iotvertebrae/modules/hardware/pcbDesign/fabAdcRib/pdf/rib4inAd_00-B_Silkscreen.pdf

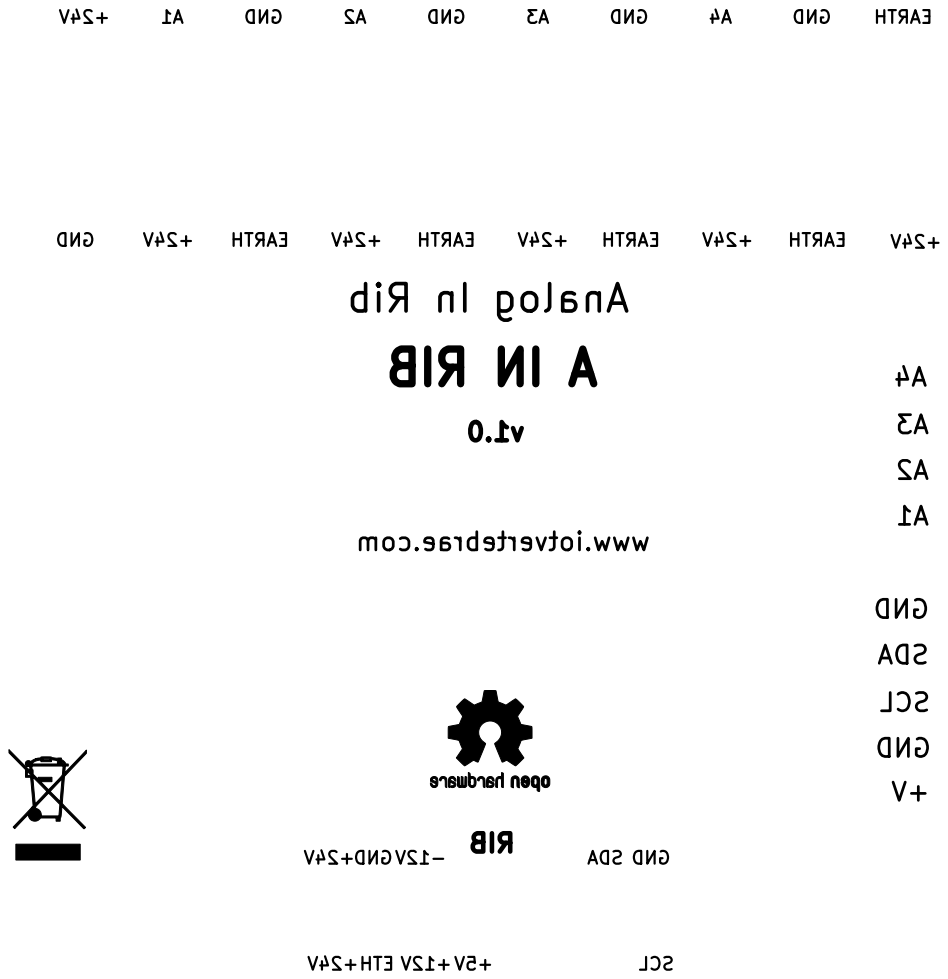
[picture p6: page 1]

GND EARTH A4 SDA GND

GND +VGND Analog In Rib
