iotvertebrae/modules/hardware/pcbDesign/fabAnalogVertebra/pdf/vertExpI2c_00-B_Silkscreen.pdf

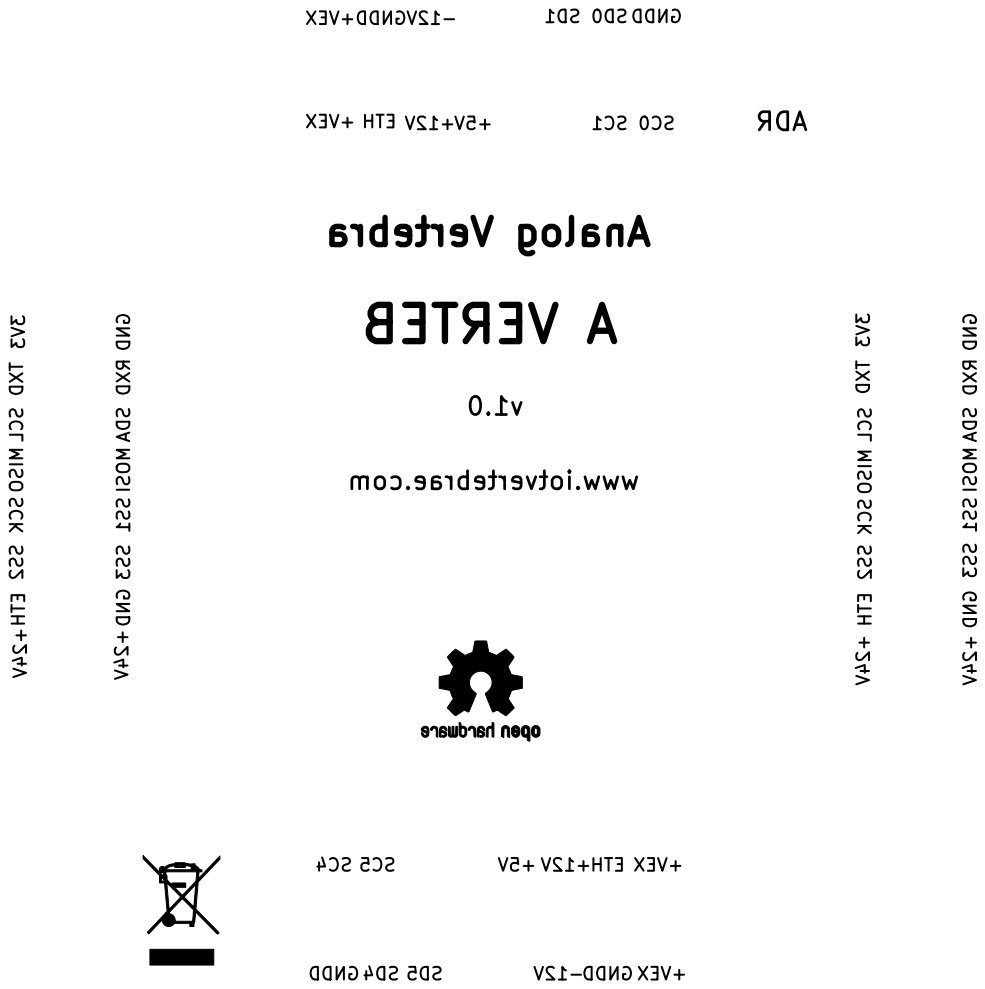
[picture p7: page 1]

+VEX A VERTEB GND ETH SS1 +VEX RXD SS2 GNDD 3V3 3V3 +24V GNDD MOSI SDA TXD +24V ADR

Analog Vertebra MOSI SCL www.iotvertebrae.com
