iotvertebrae/modules/hardware/pcbDesign/fabDacRib/pdf/rib4outAd_00-B_Silkscreen.pdf

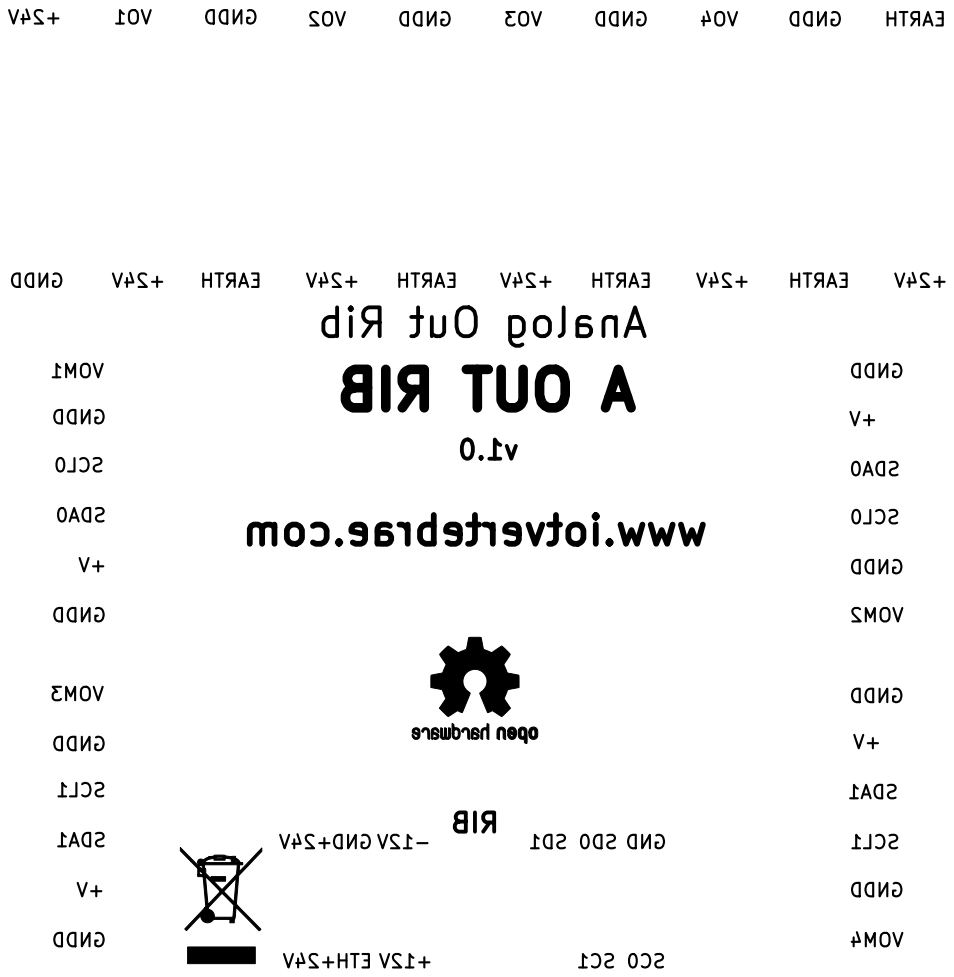
[picture p8: page 1]

SD1 SCL0 GNDD Analog Out Rib

ETH www.iotvertebrae.com
