iotvertebrae/modules/hardware/pcbDesign/v2.0/gerbers/avert20/pdf/avert_12-B_Silkscreen.pdf

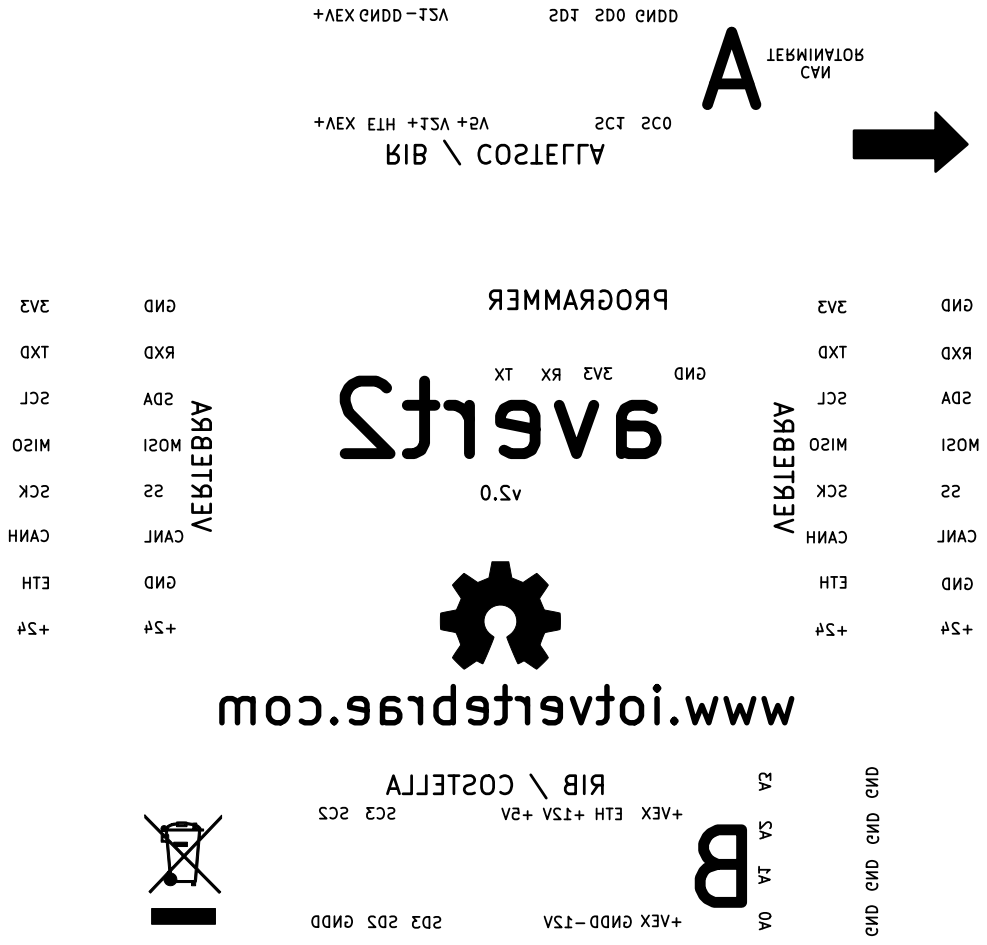
[picture p9: page 1]

+VEX PROGRAMMER GND GND

COSTELLA / RIB VERTEBRA VERTEBRA

+12V A2 GNDD www.iotvertebrae.com
