iotvertebrae/modules/hardware/pcbDesign/fabDigitalInputRib/pdf/rib8in_00-Edge_Cuts.pdf

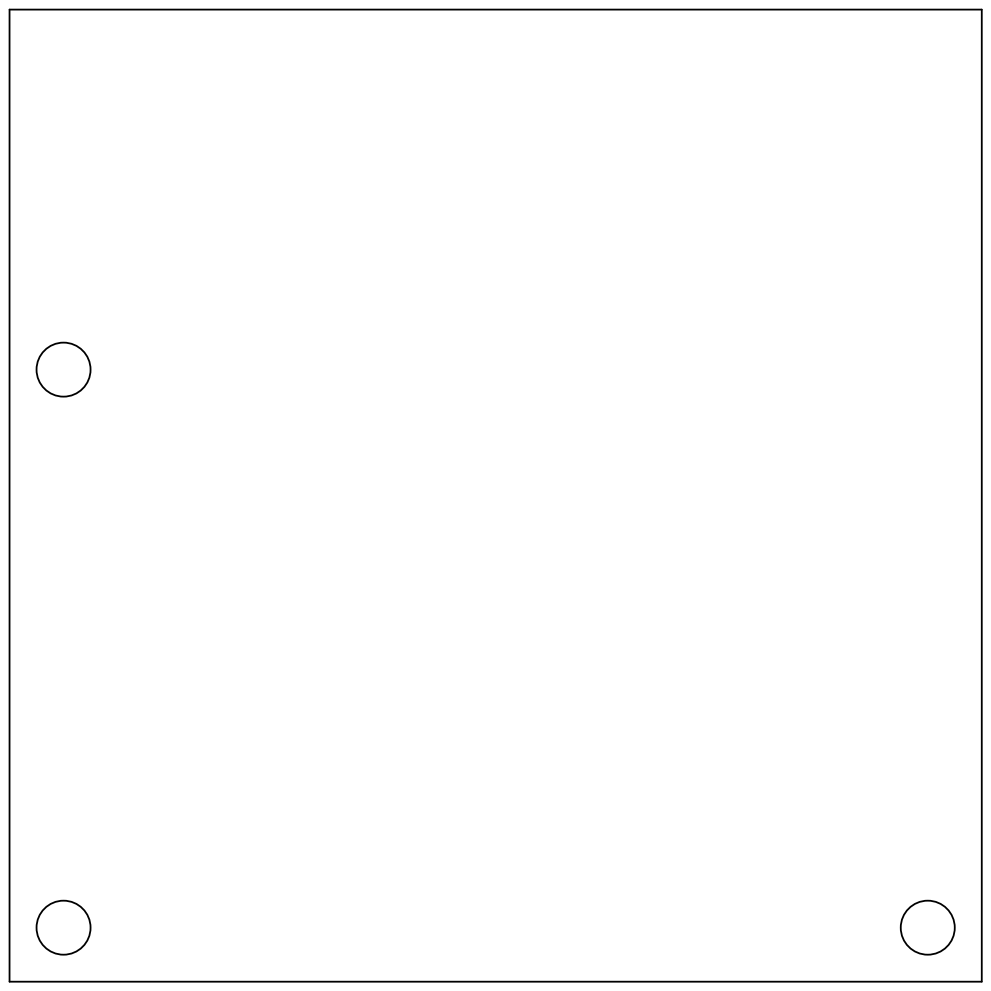
[picture p18: page 1]
