iotvertebrae/modules/hardware/pcbDesign/fabDigitalInputRib/pdf/rib8in_00-F_Cu.pdf

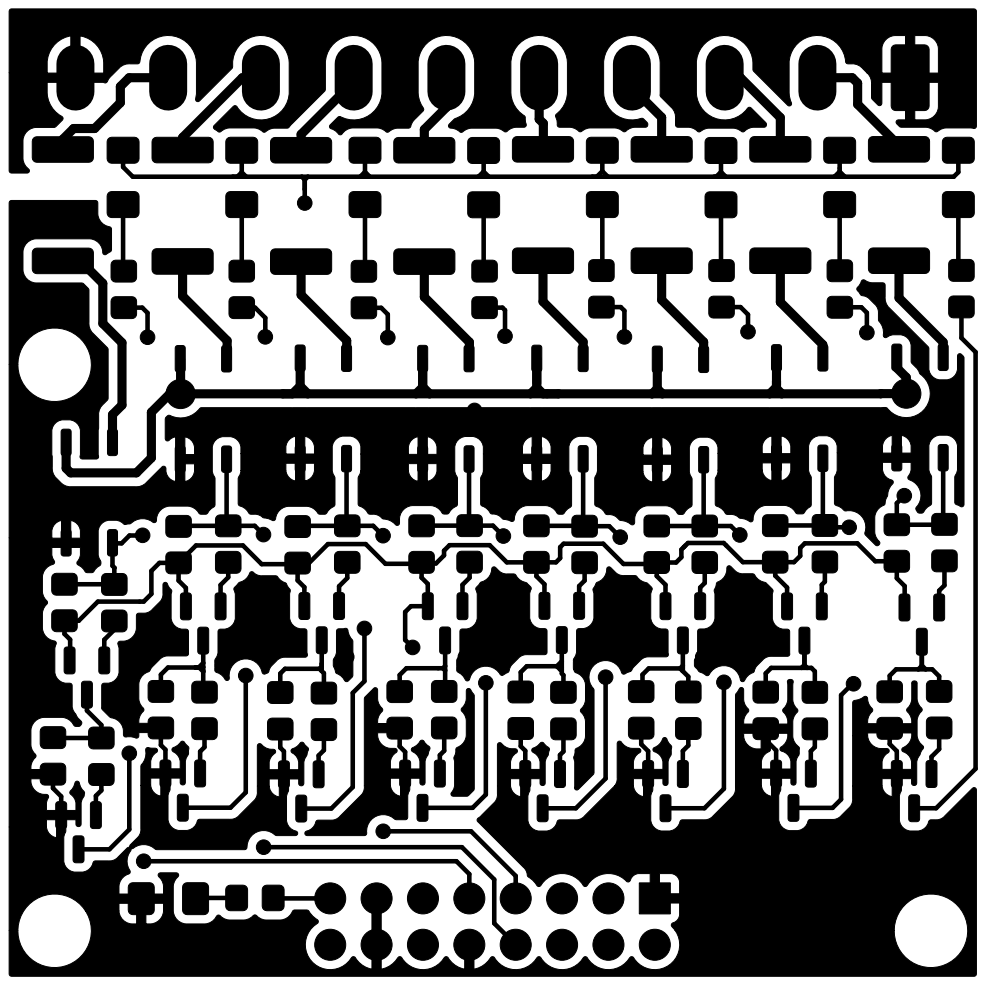
[picture p19: page 1]
