iotvertebrae/modules/hardware/pcbDesign/fabDigitalInputRib/pdf/rib8in_00-F_Mask.pdf

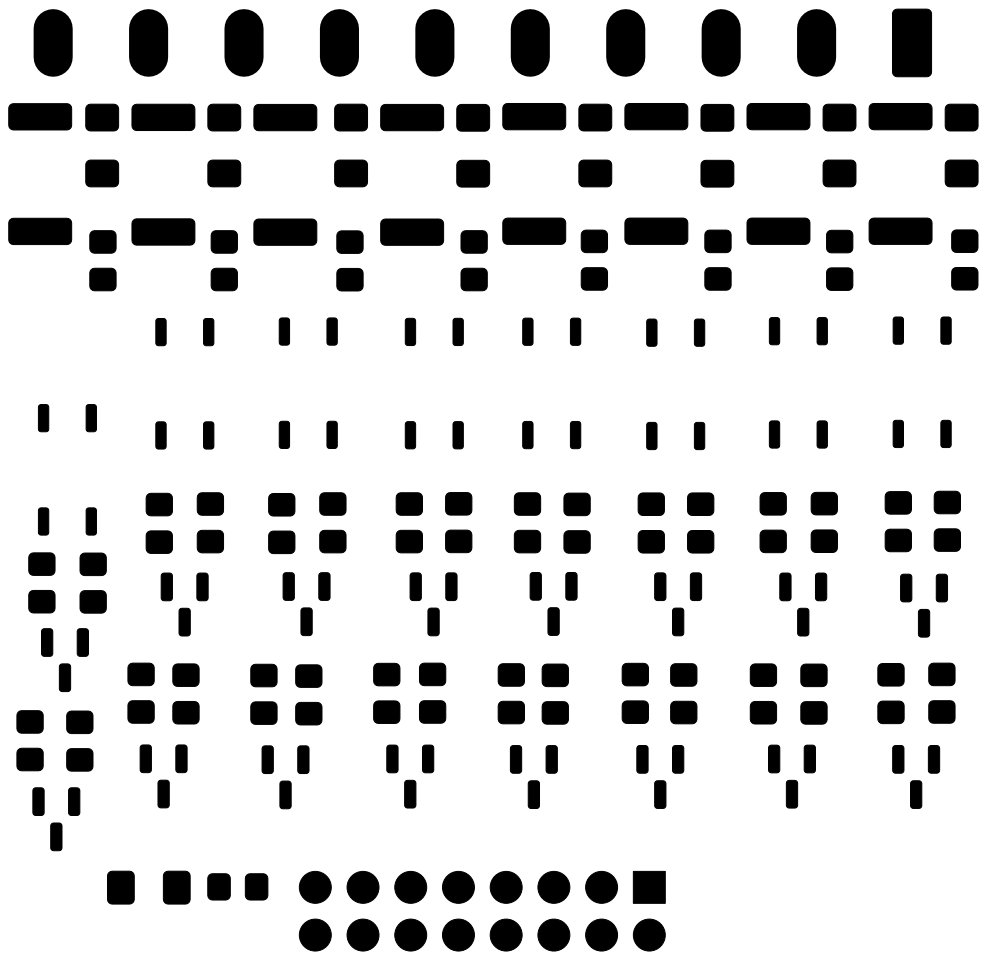
[picture p20: page 1]
