iotvertebrae/modules/hardware/pcbDesign/fabDigitalInputRib/pdf/rib8in_00-F_Paste.pdf

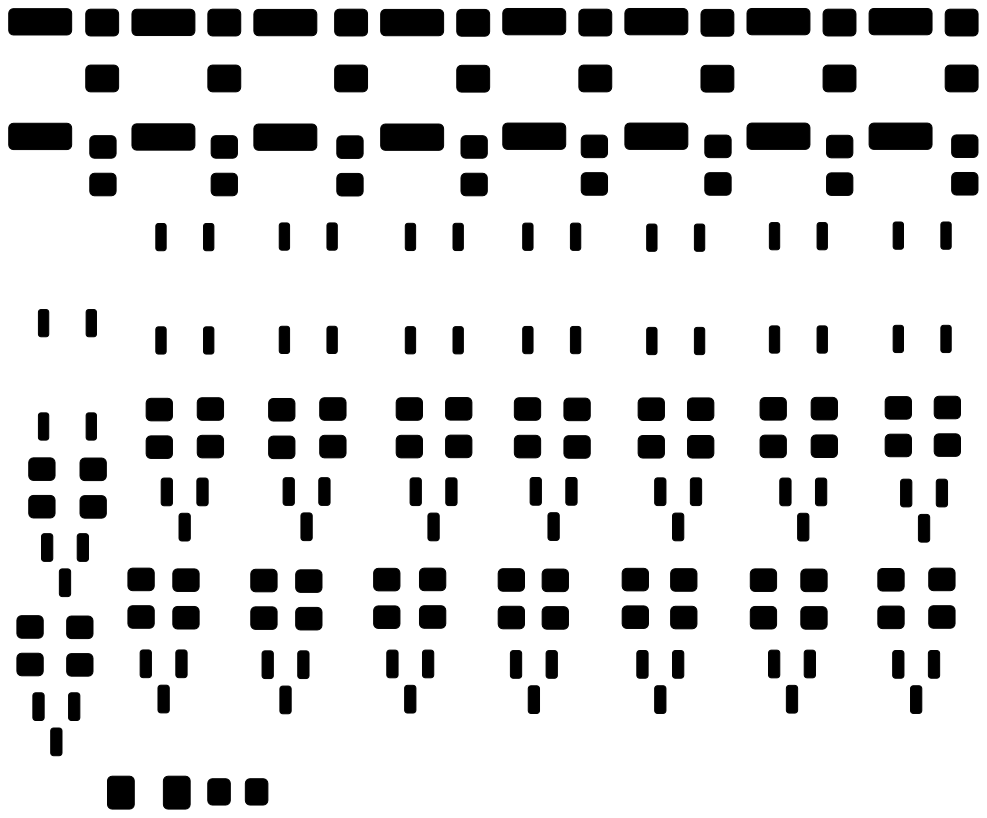
[picture p21: page 1]
