iotvertebrae/modules/hardware/pcbDesign/fabDigitalInputRib/pdf/rib8in_00-F_Silkscreen.pdf

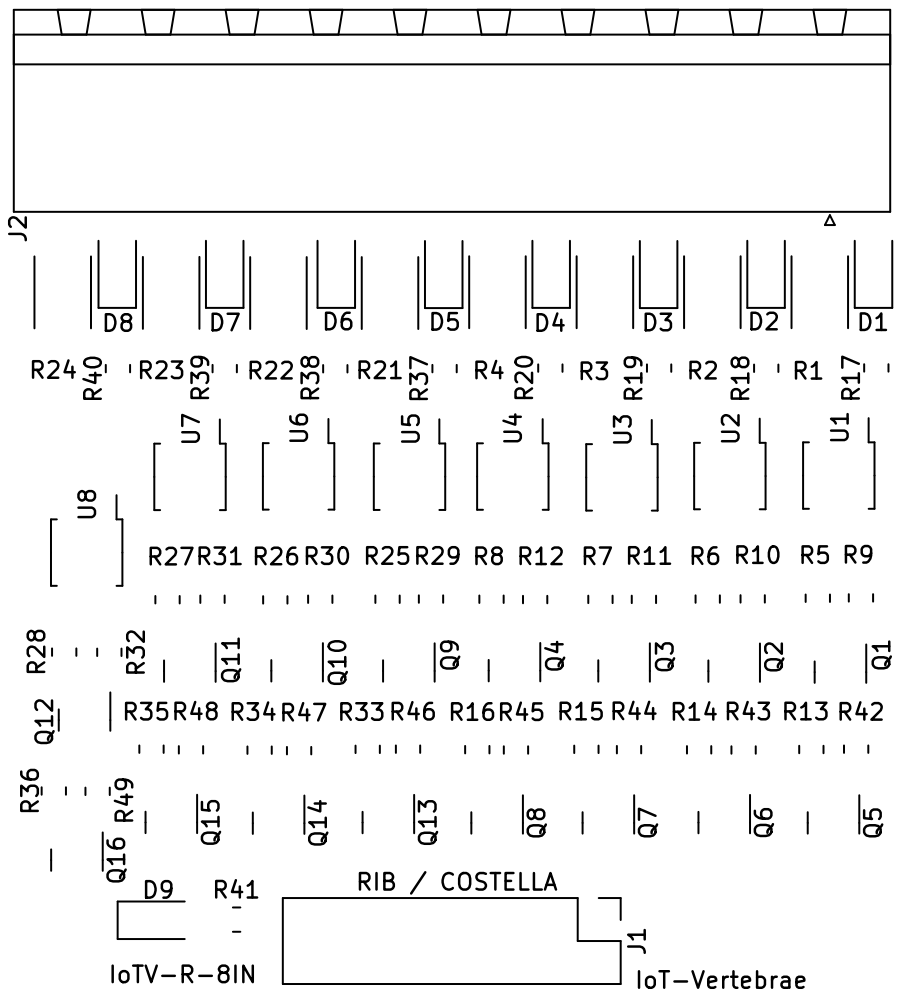
[picture p22: page 1]
