iotvertebrae/modules/hardware/pcbDesign/fabDigitalOutputRib/pdf/rib6out_01-B_Cu.pdf

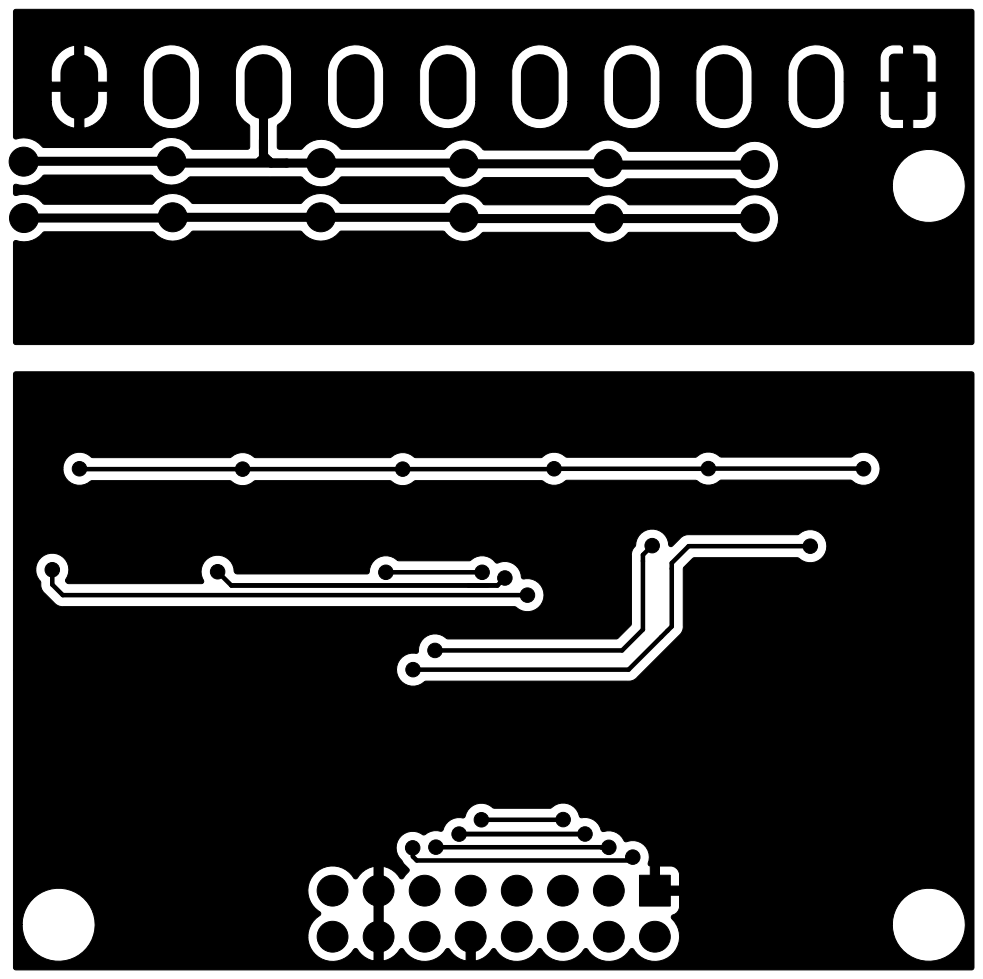
[picture p23: page 1]
