iotvertebrae/modules/hardware/pcbDesign/fabDigitalOutputRib/pdf/rib6out_01-B_Mask.pdf

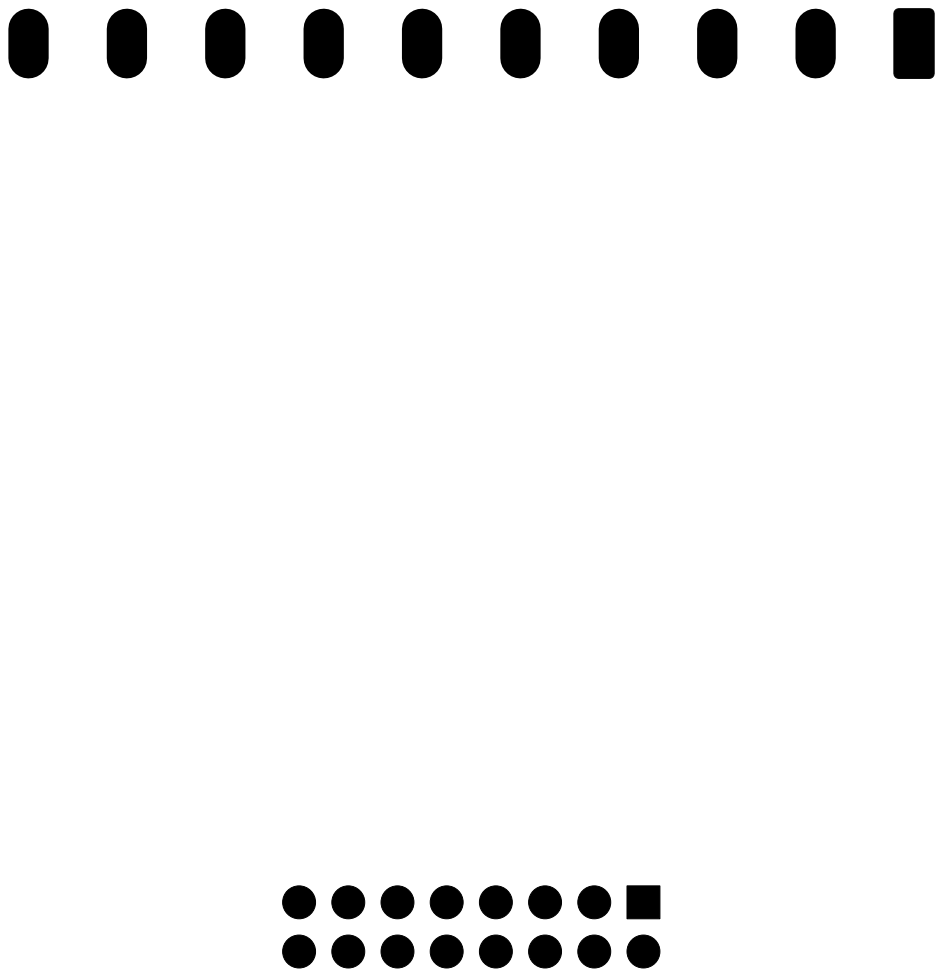
[picture p24: page 1]
