iotvertebrae/modules/hardware/pcbDesign/fabDigitalOutputRib/pdf/rib6out_01-Edge_Cuts.pdf

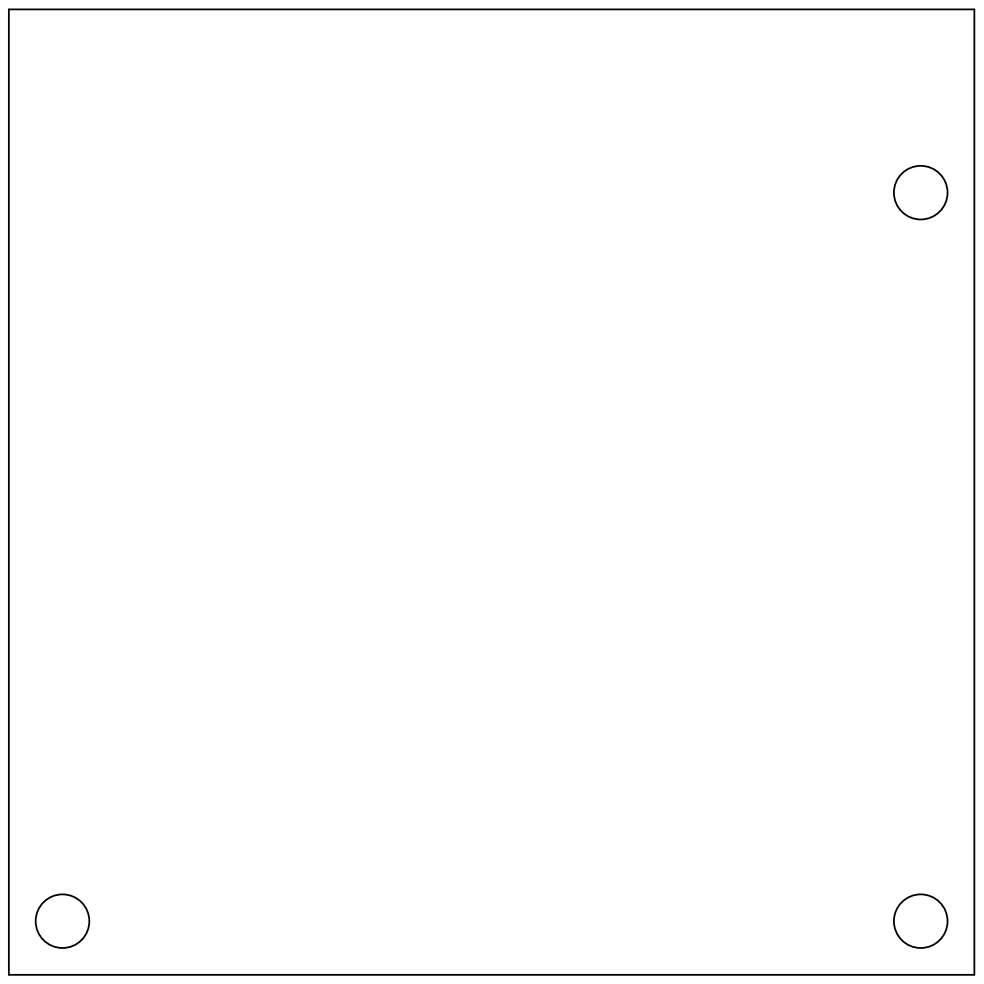
[picture p25: page 1]
