iotvertebrae/modules/hardware/pcbDesign/fabDigitalOutputRib/pdf/rib6out_01-F_Cu.pdf

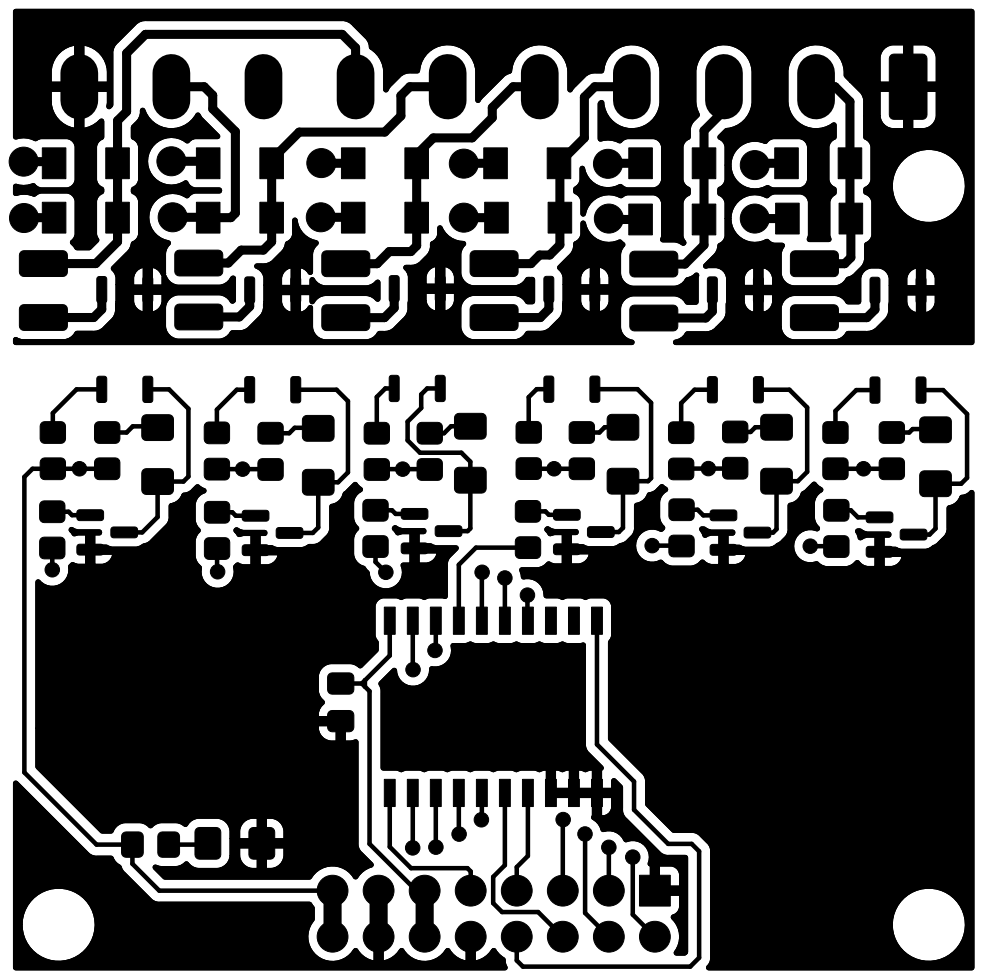
[picture p26: page 1]
