iotvertebrae/modules/hardware/pcbDesign/fabDigitalOutputRib/pdf/rib6out_01-F_Mask.pdf

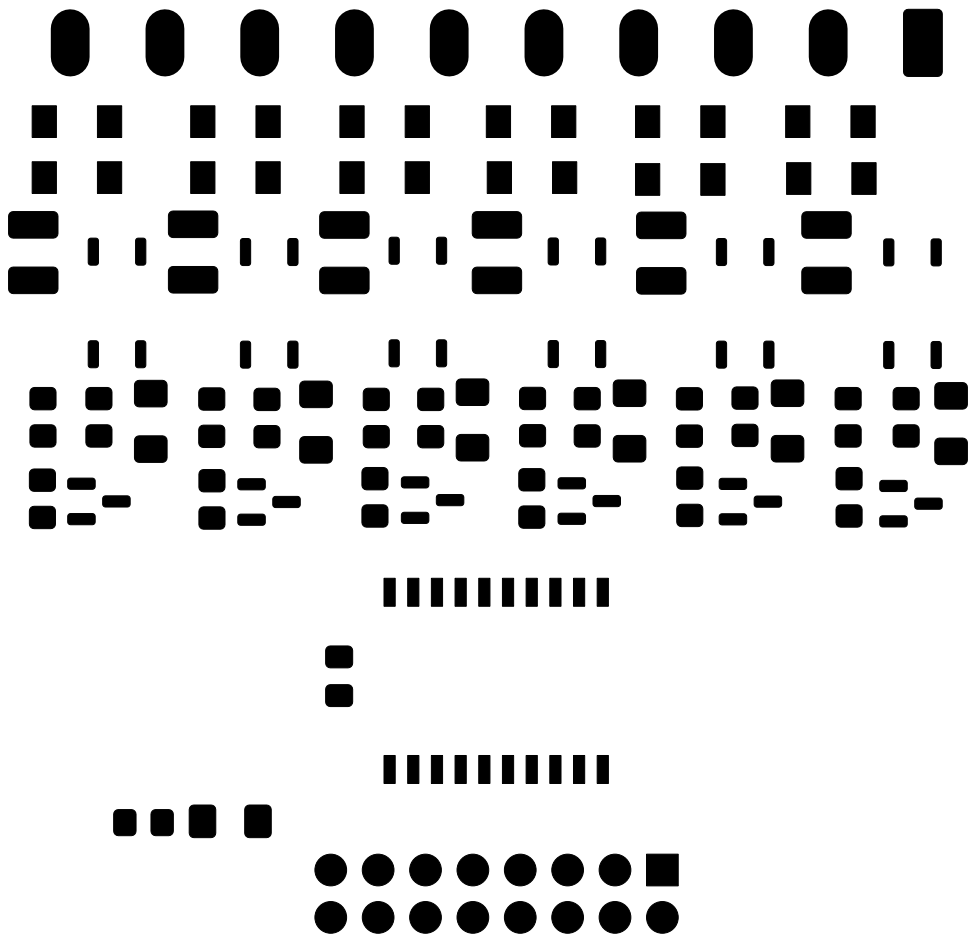
[picture p27: page 1]
