iotvertebrae/modules/hardware/pcbDesign/fabDigitalOutputRib/pdf/rib6out_01-F_Paste.pdf

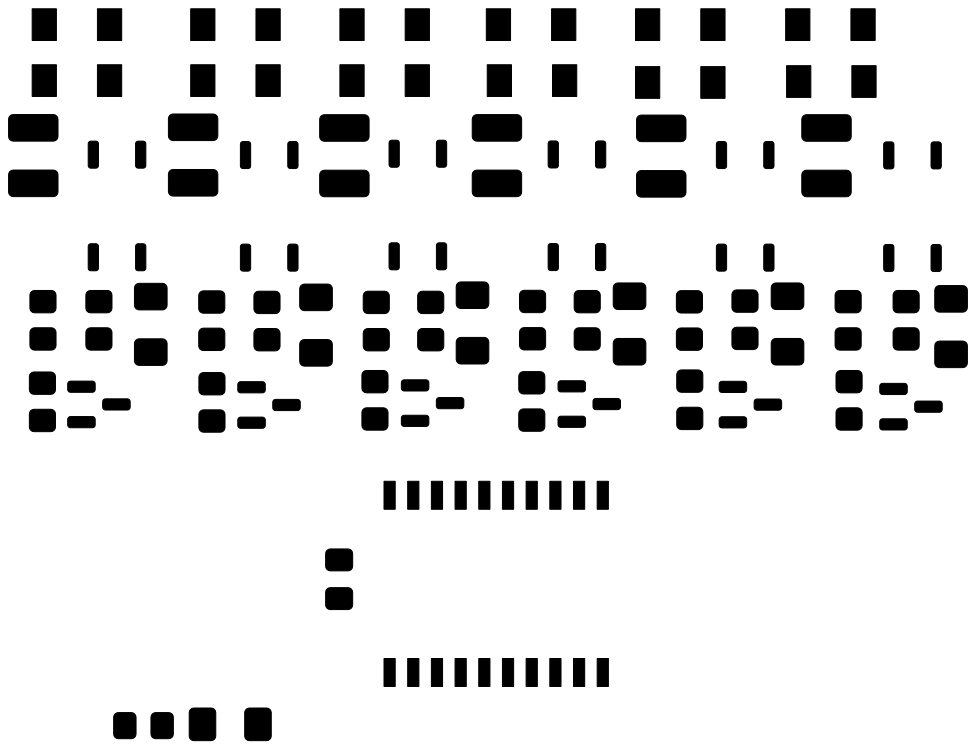
[picture p28: page 1]
