iotvertebrae/modules/hardware/pcbDesign/fabDigitalOutputRib/pdf/rib6out_01-F_Silkscreen.pdf

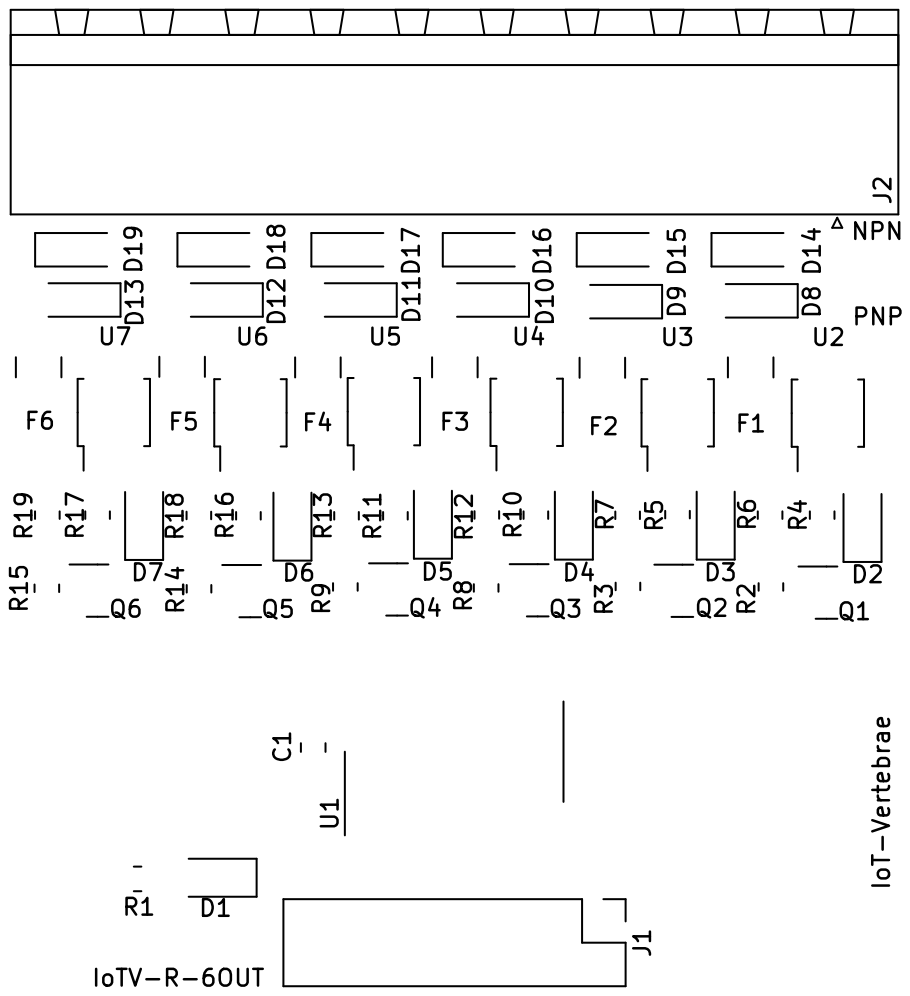
[picture p29: page 1]
