iotvertebrae/modules/hardware/pcbDesign/fabDigitalVertebra/pdf/vertExpIO_00-B_Cu.pdf

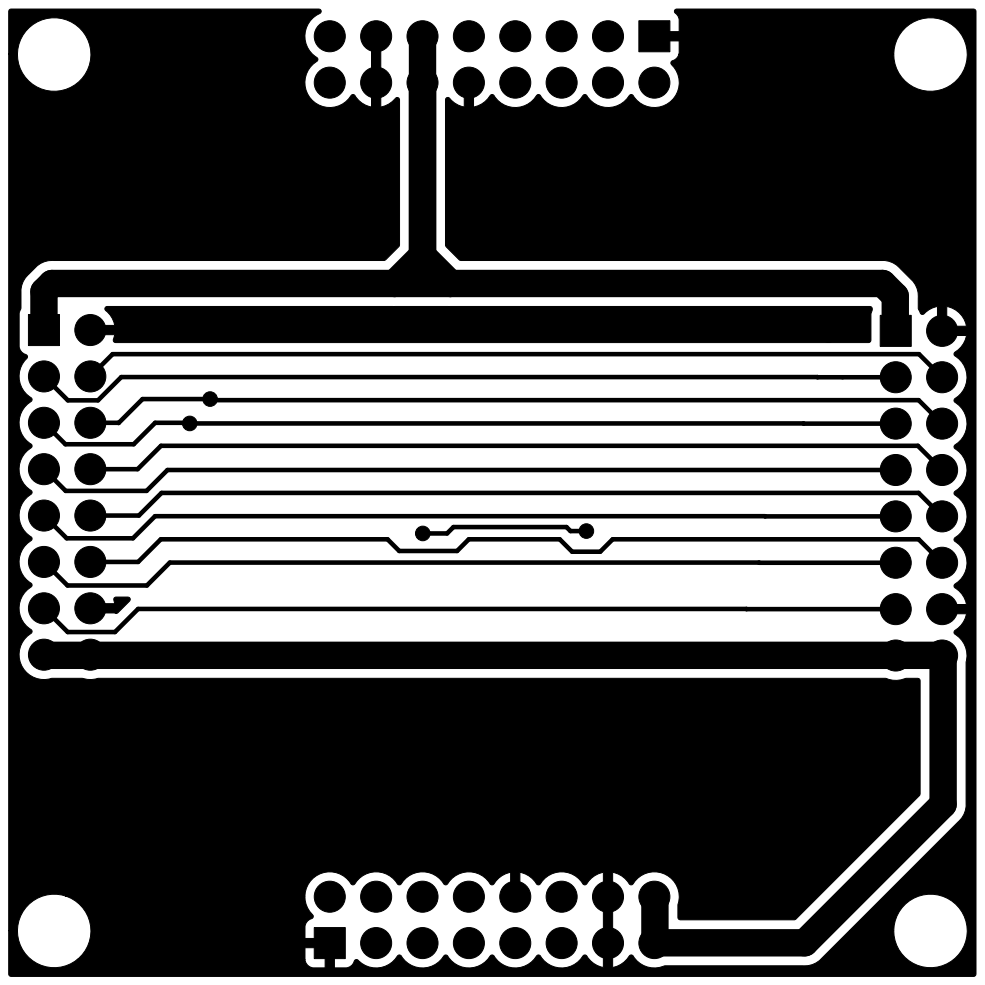
[picture p30: page 1]
