iotvertebrae/modules/hardware/pcbDesign/fabDigitalVertebra/pdf/vertExpIO_00-B_Mask.pdf

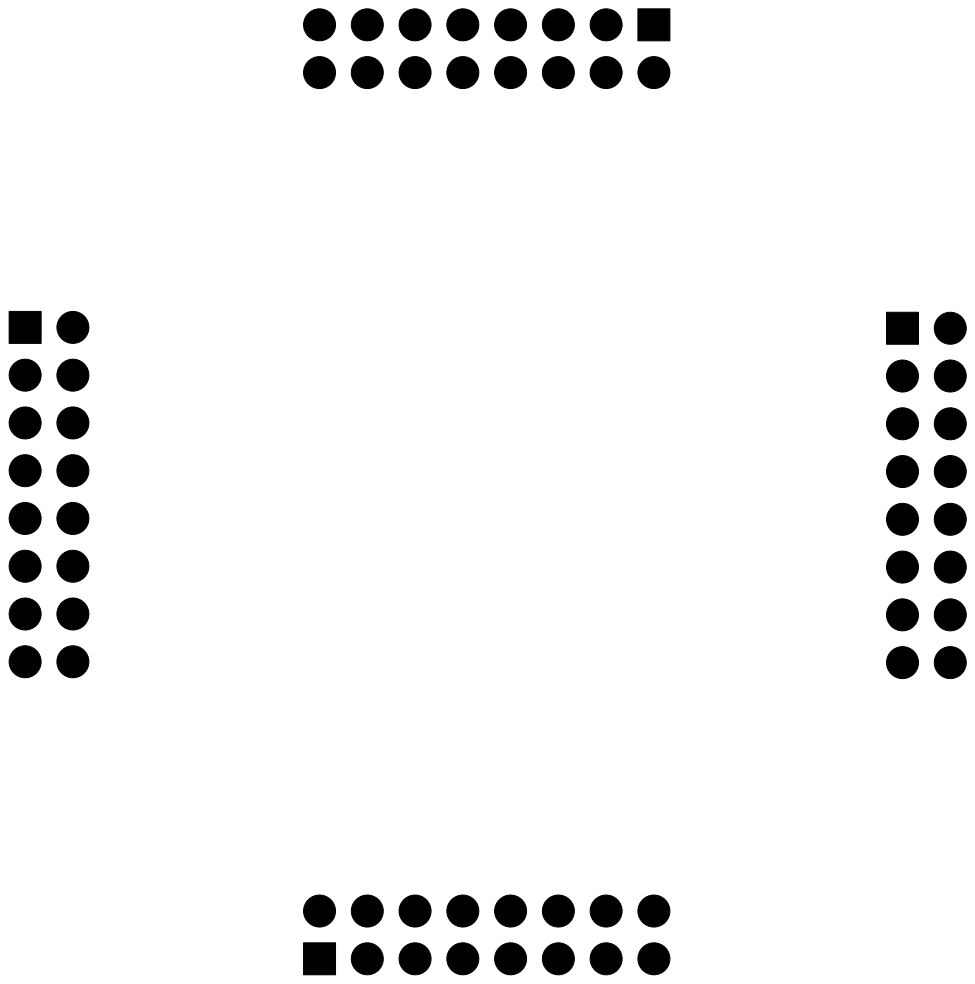
[picture p31: page 1]
