iotvertebrae/modules/hardware/pcbDesign/fabDigitalVertebra/pdf/vertExpIO_00-Edge_Cuts.pdf

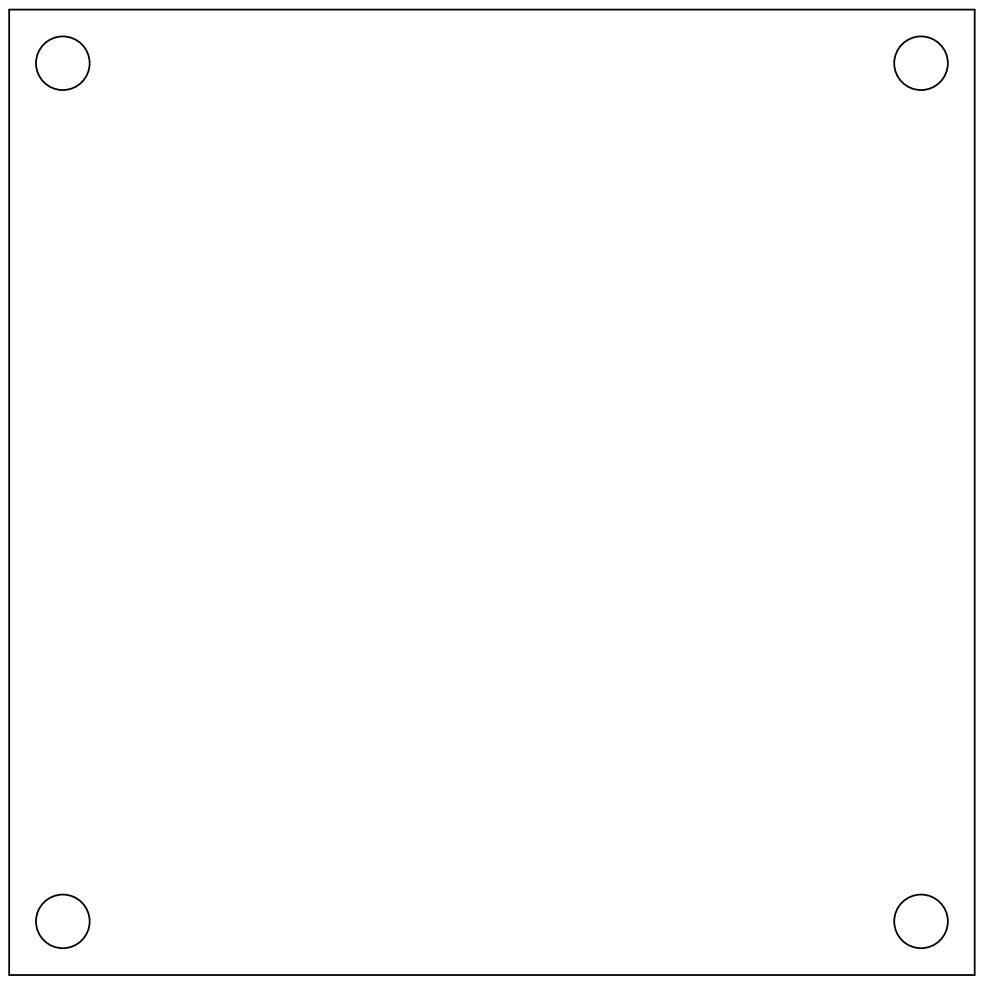
[picture p32: page 1]
