iotvertebrae/modules/hardware/pcbDesign/fabDigitalVertebra/pdf/vertExpIO_00-F_Cu.pdf

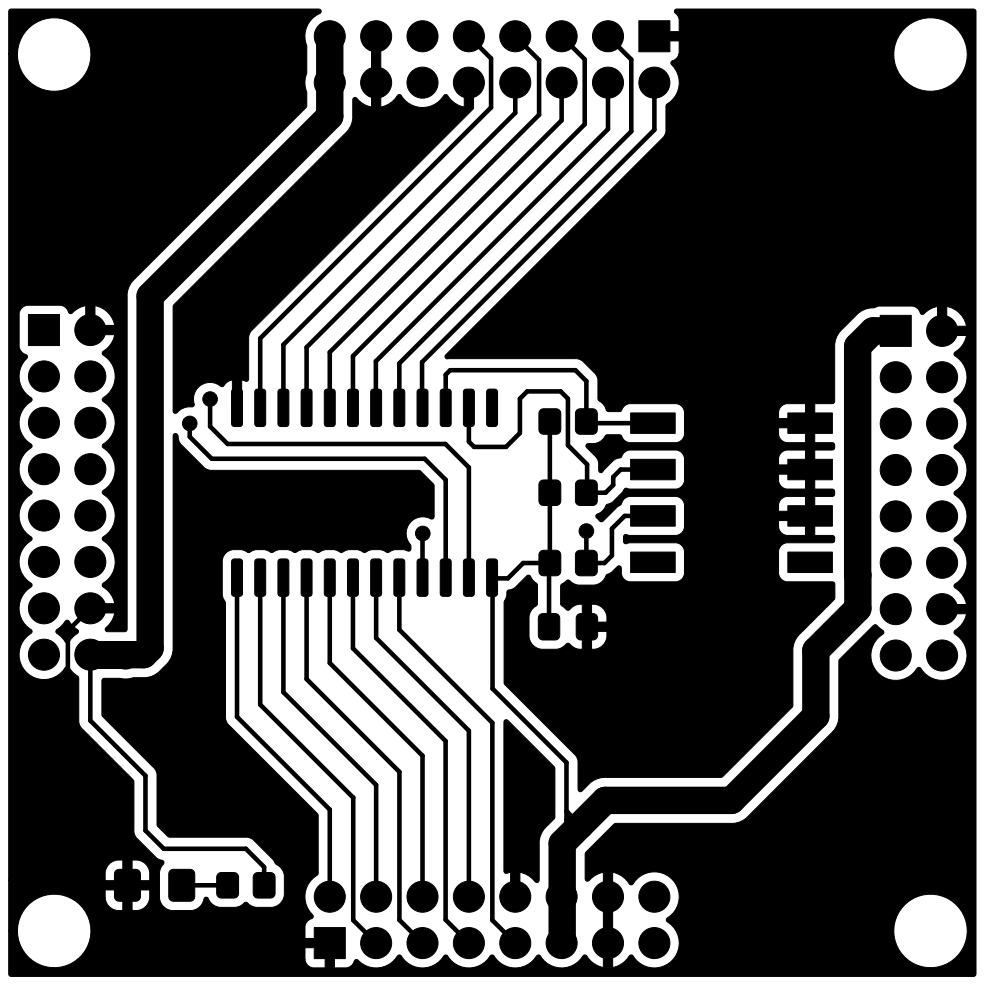
[picture p33: page 1]
