iotvertebrae/modules/hardware/pcbDesign/fabDigitalVertebra/pdf/vertExpIO_00-F_Mask.pdf

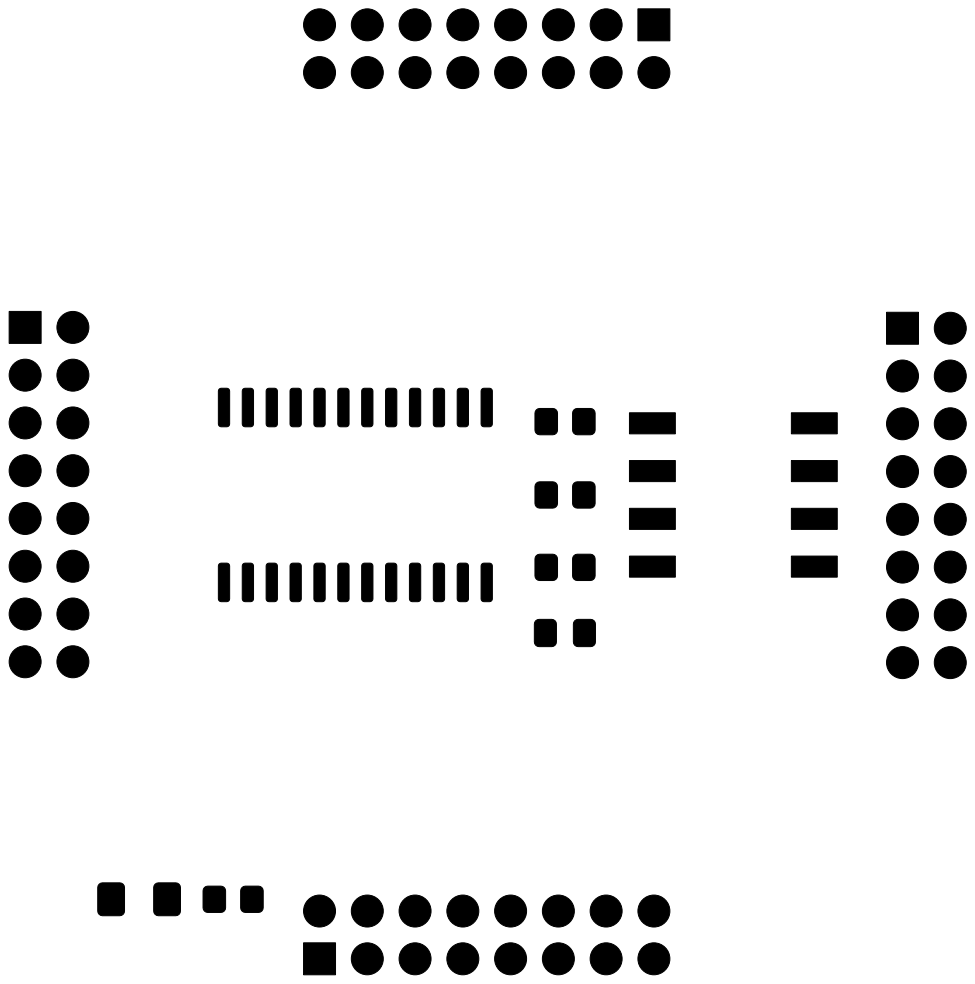
[picture p34: page 1]
