iotvertebrae/modules/hardware/pcbDesign/fabDigitalVertebra/pdf/vertExpIO_00-F_Paste.pdf

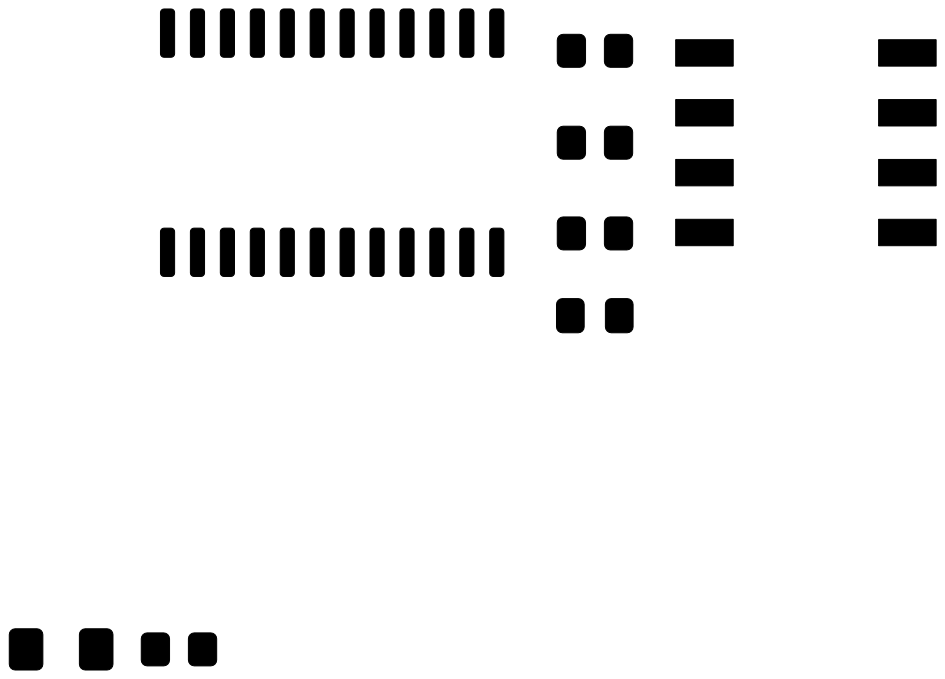
[picture p35: page 1]
