iotvertebrae/modules/hardware/pcbDesign/fabDigitalVertebra/pdf/vertExpIO_00-F_Silkscreen.pdf

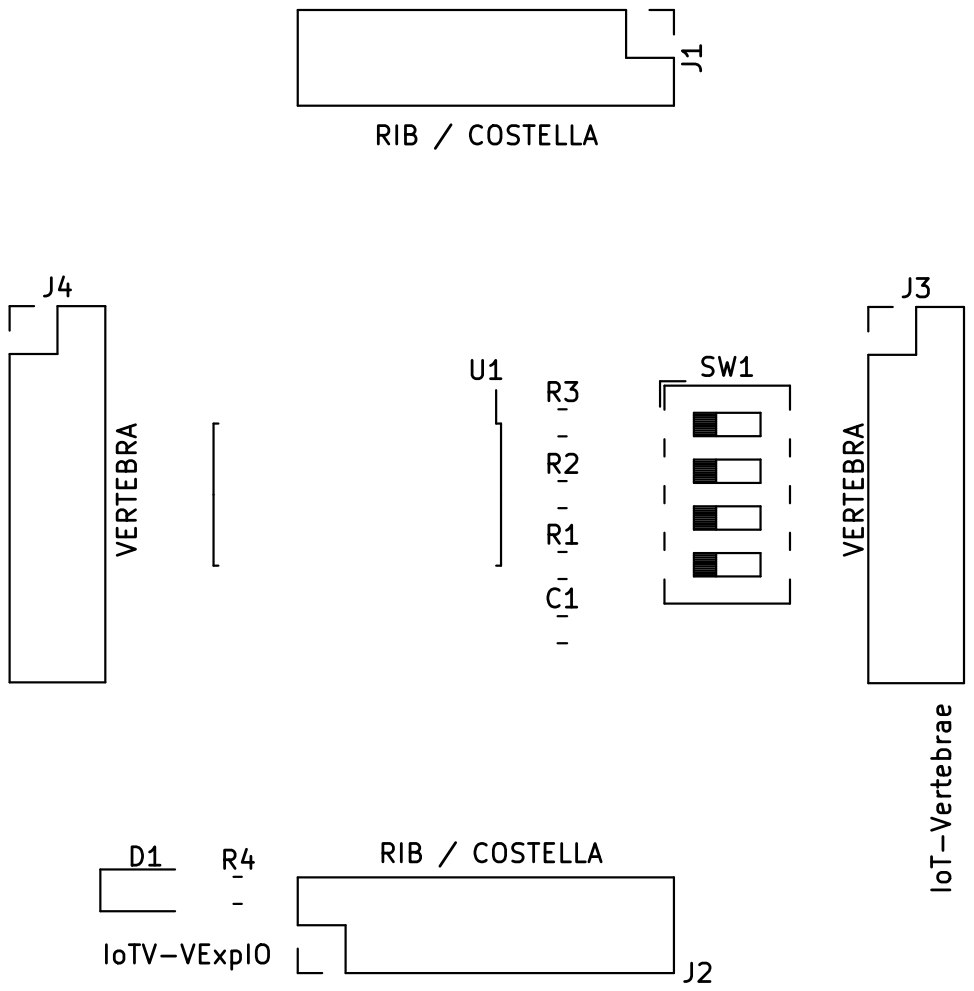
[picture p36: page 1]
