iotvertebrae/modules/hardware/pcbDesign/fabAdcRib/pdf/rib4inAd_00-B_Cu.pdf

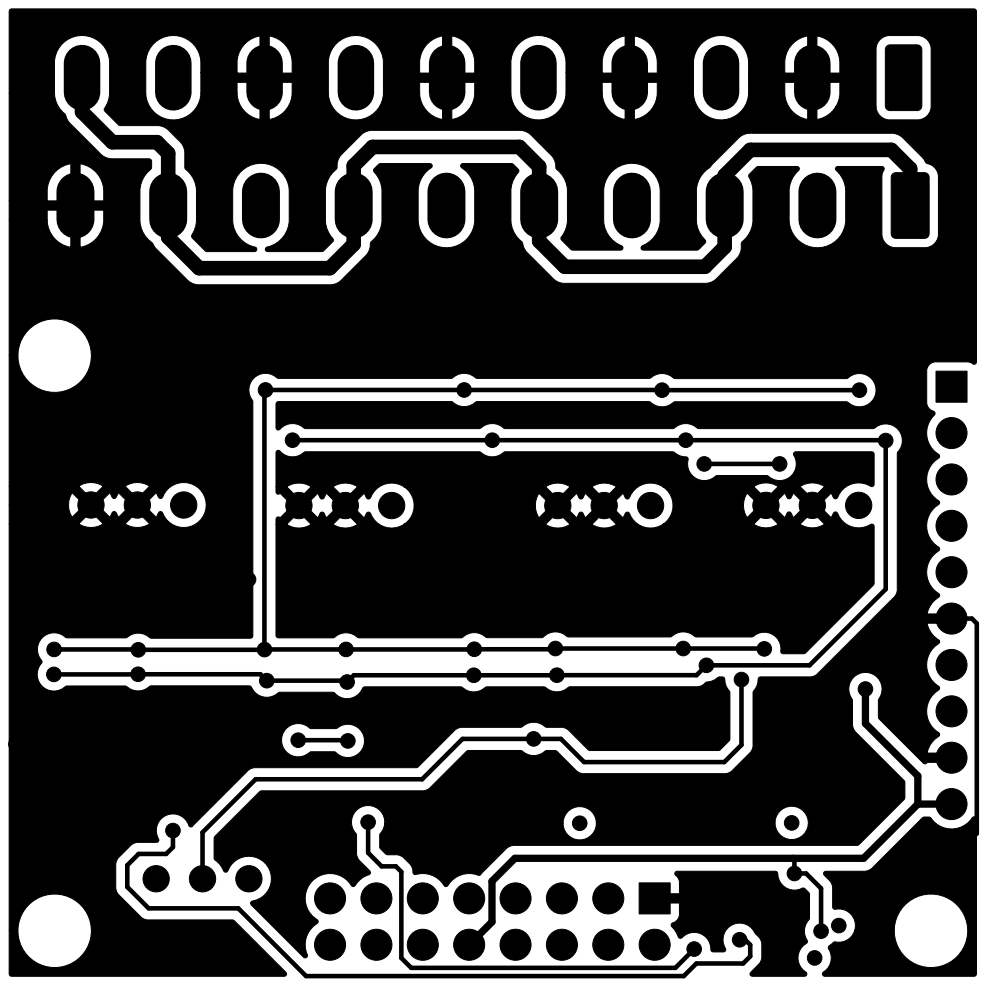
[picture p37: page 1]
