iotvertebrae/modules/hardware/pcbDesign/fabAdcRib/pdf/rib4inAd_00-B_Mask.pdf

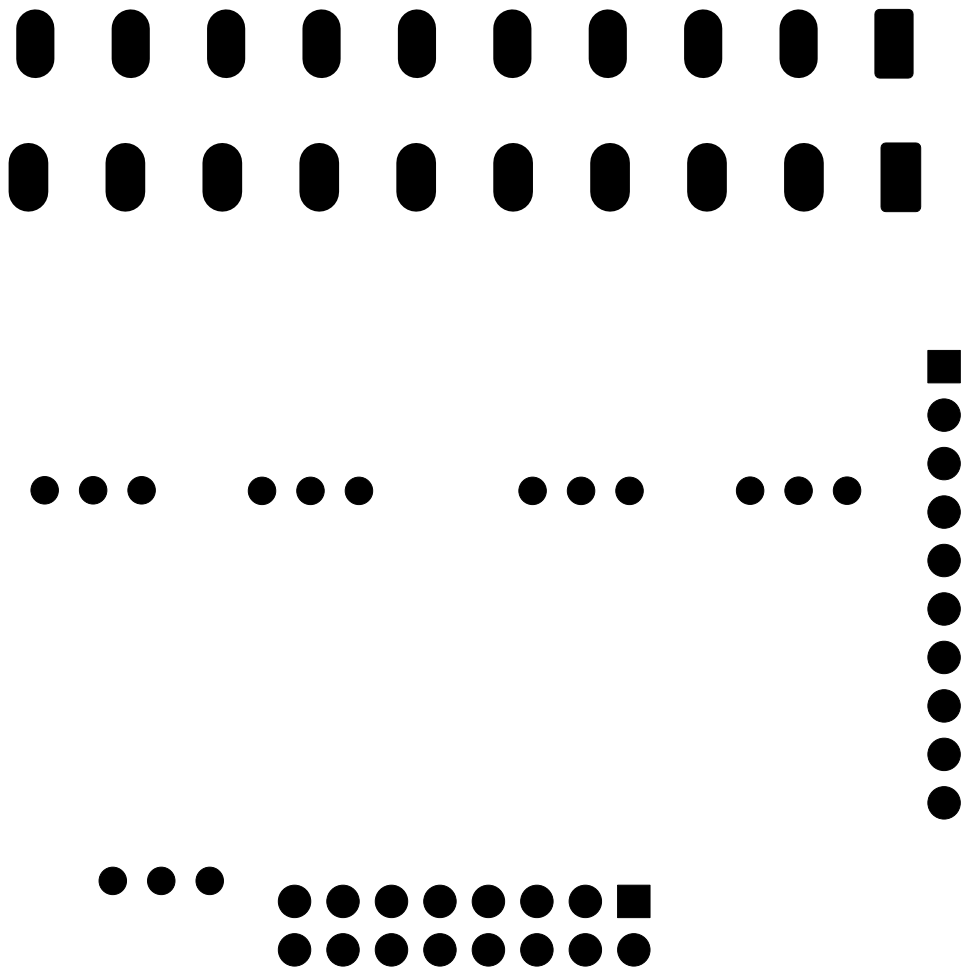
[picture p38: page 1]
