iotvertebrae/modules/hardware/pcbDesign/fabAdcRib/pdf/rib4inAd_00-Edge_Cuts.pdf

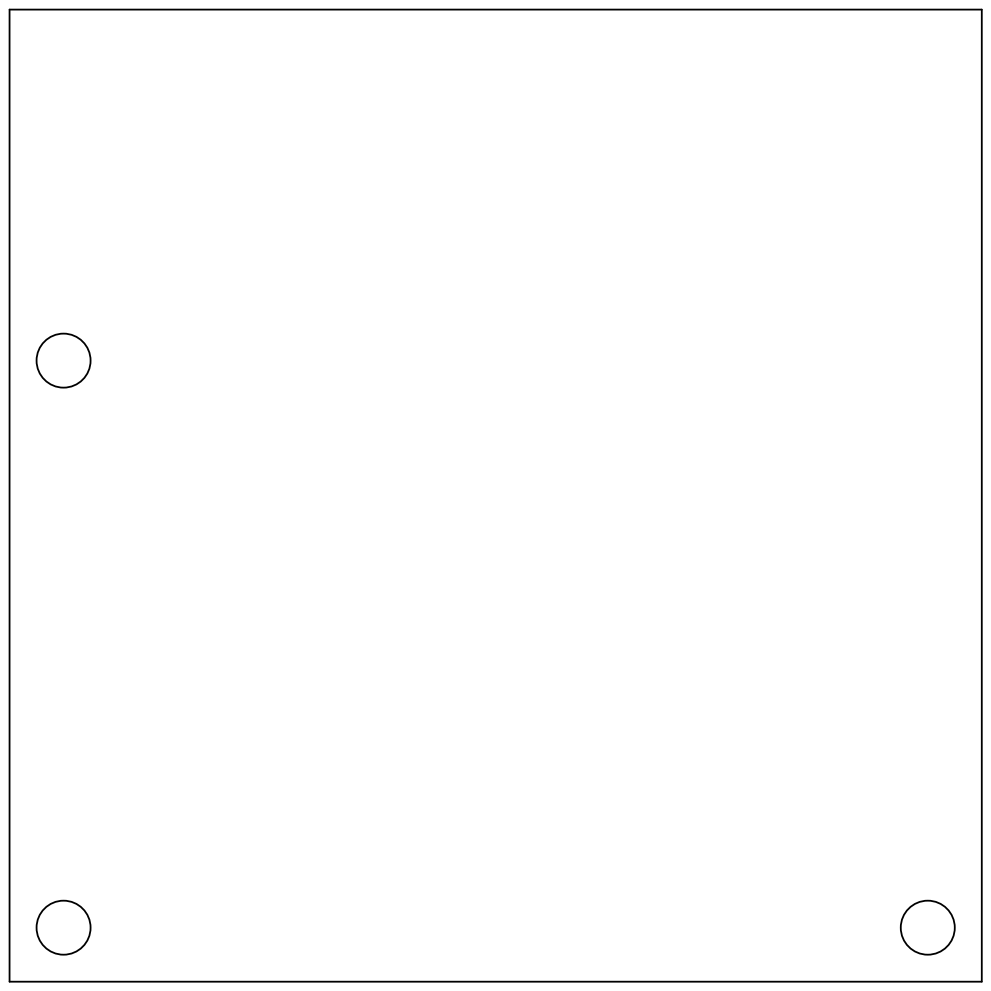
[picture p39: page 1]
