iotvertebrae/modules/hardware/pcbDesign/fabAdcRib/pdf/rib4inAd_00-F_Cu.pdf

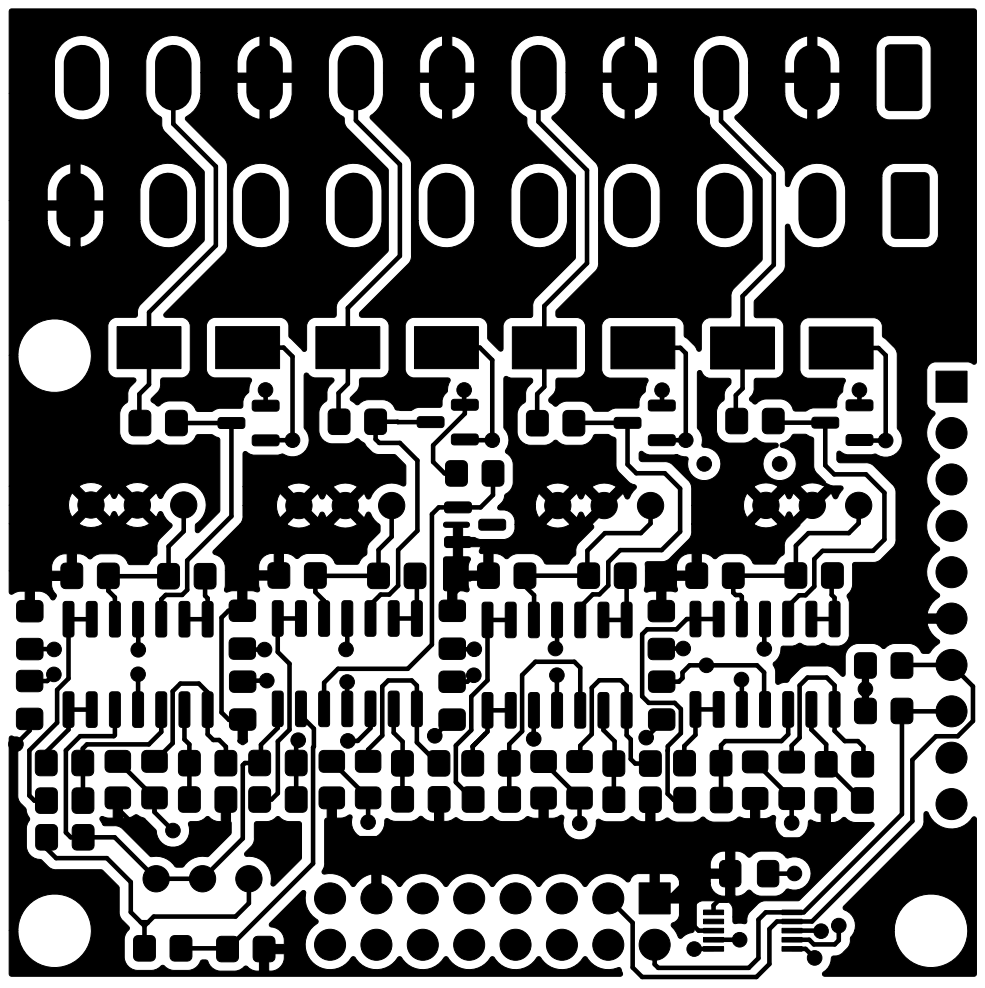
[picture p40: page 1]
