iotvertebrae/modules/hardware/pcbDesign/fabAdcRib/pdf/rib4inAd_00-F_Mask.pdf

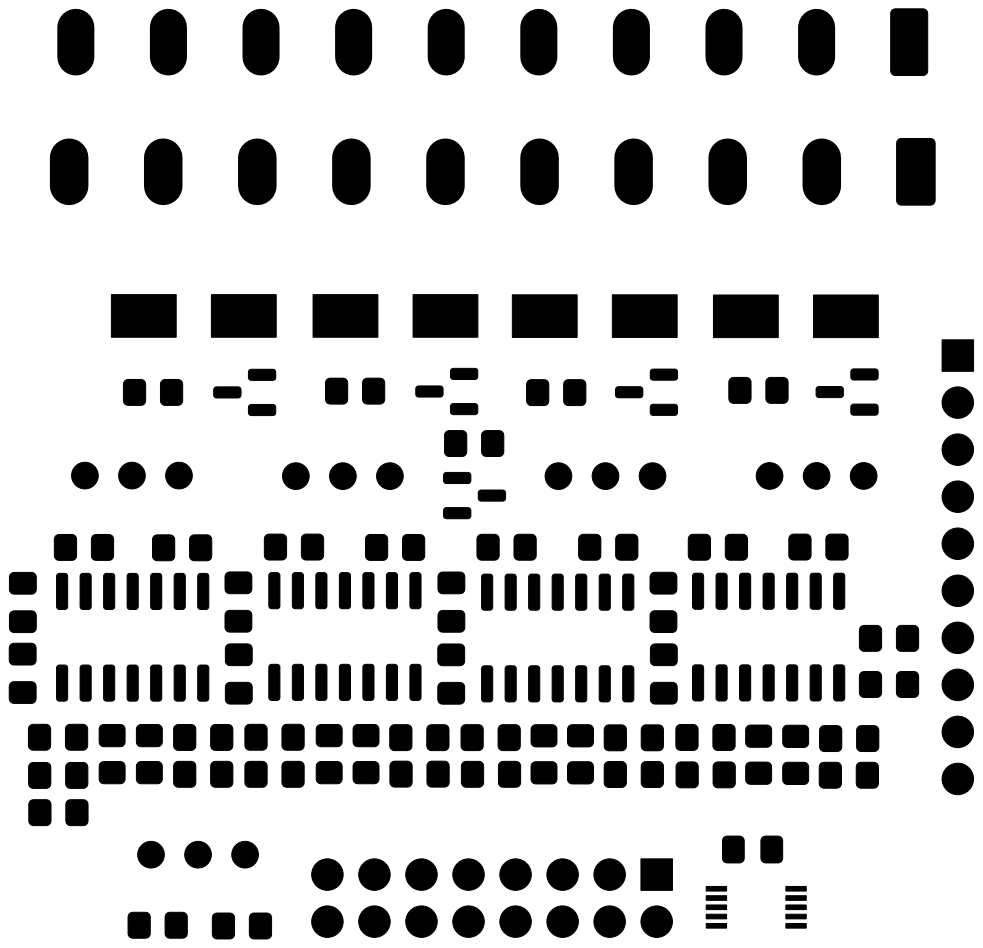
[picture p41: page 1]
