iotvertebrae/modules/hardware/pcbDesign/fabAdcRib/pdf/rib4inAd_00-F_Paste.pdf

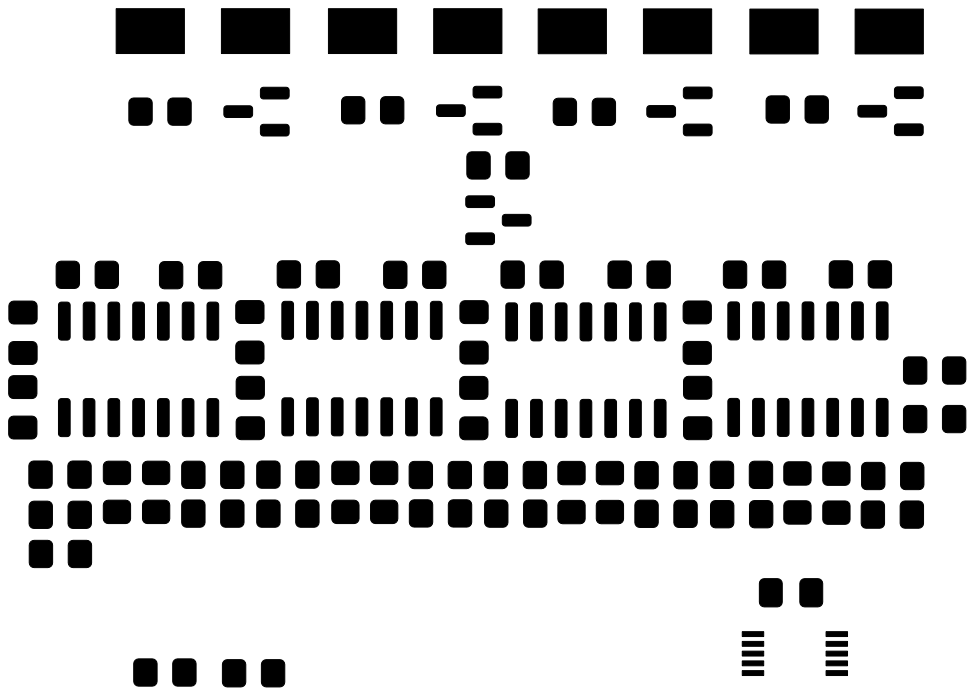
[picture p42: page 1]
