iotvertebrae/modules/hardware/pcbDesign/fabAdcRib/pdf/rib4inAd_00-F_Silkscreen.pdf

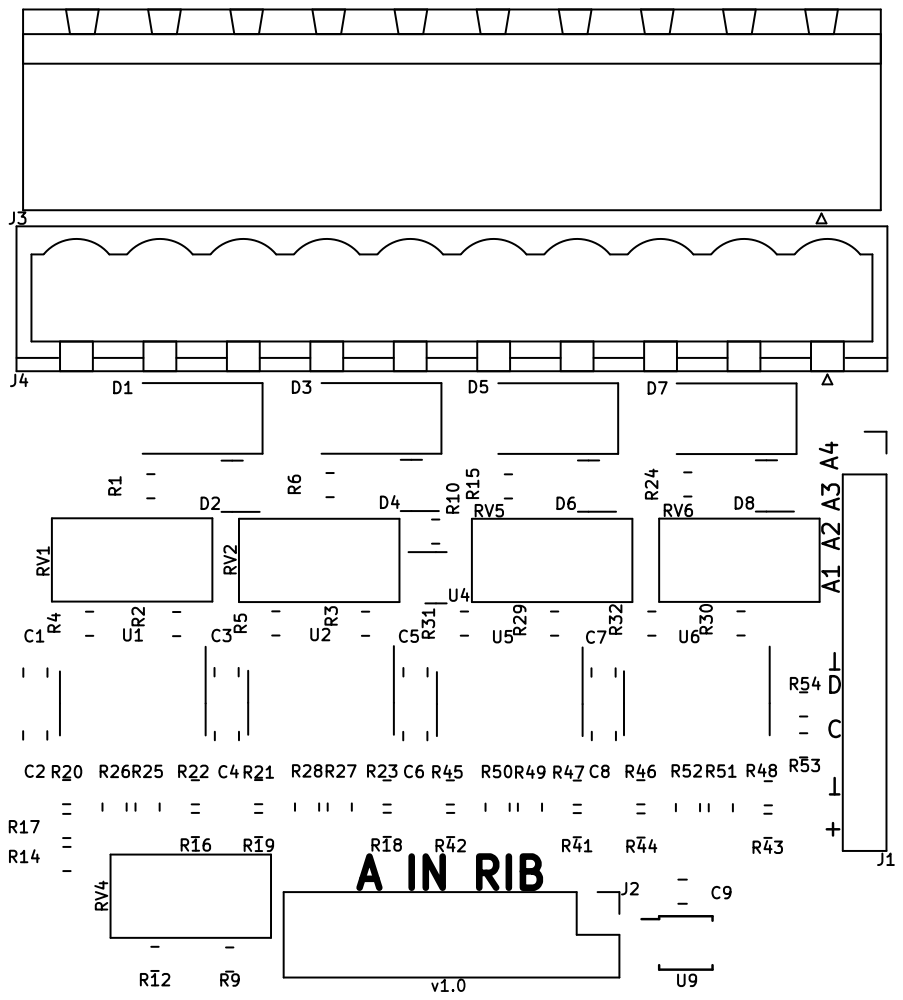
[picture p43: page 1]
