iotvertebrae/modules/hardware/pcbDesign/fabAdcRib/pdf/rib4inAd_00-In1_Cu.pdf

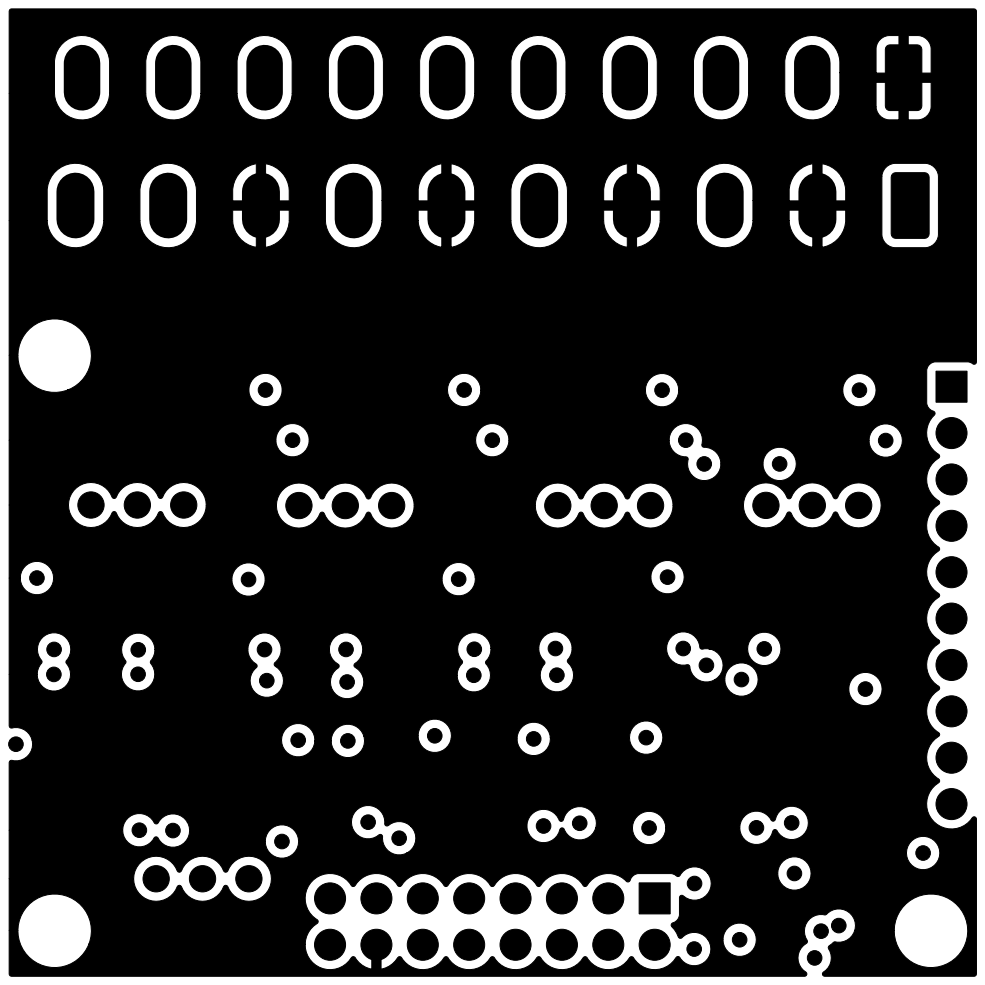
[picture p44: page 1]
