iotvertebrae/modules/hardware/pcbDesign/fabAdcRib/pdf/rib4inAd_00-In2_Cu.pdf

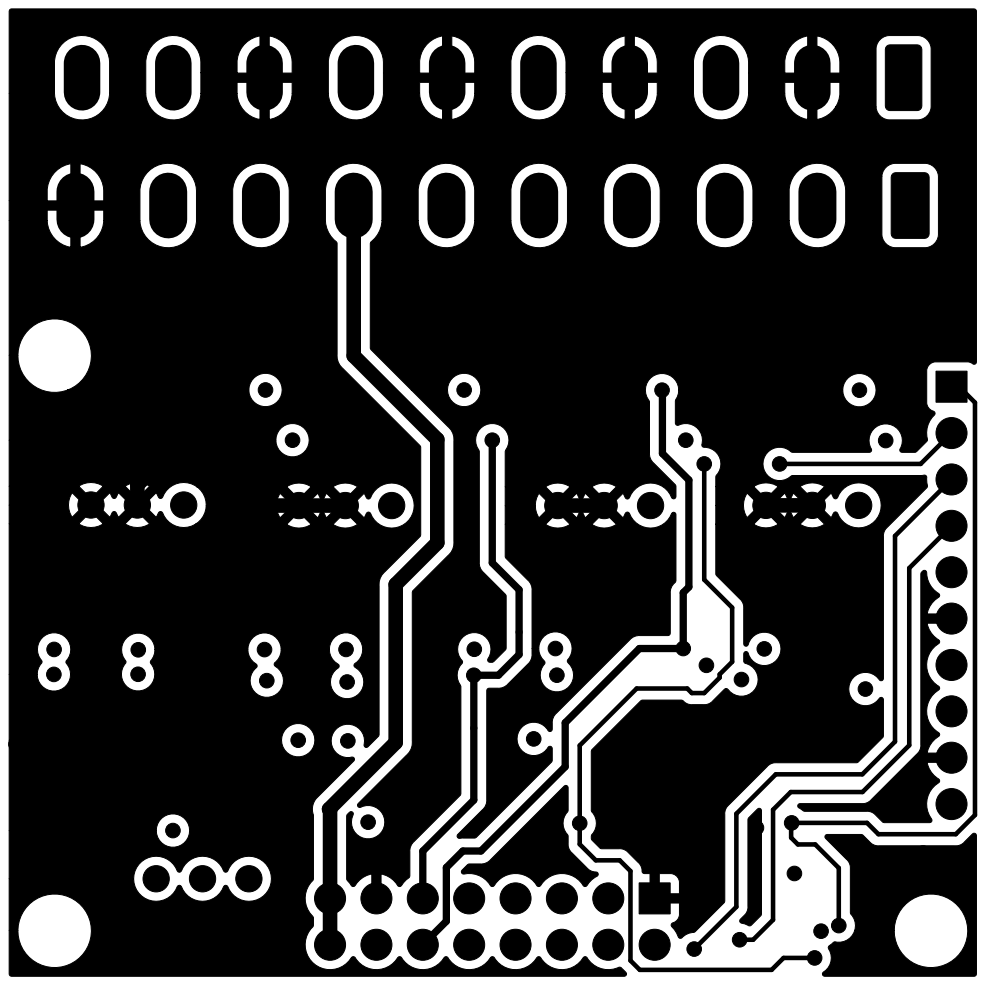
[picture p45: page 1]
