iotvertebrae/modules/hardware/pcbDesign/fabAnalogVertebra/pdf/vertExpI2c_00-B_Cu.pdf

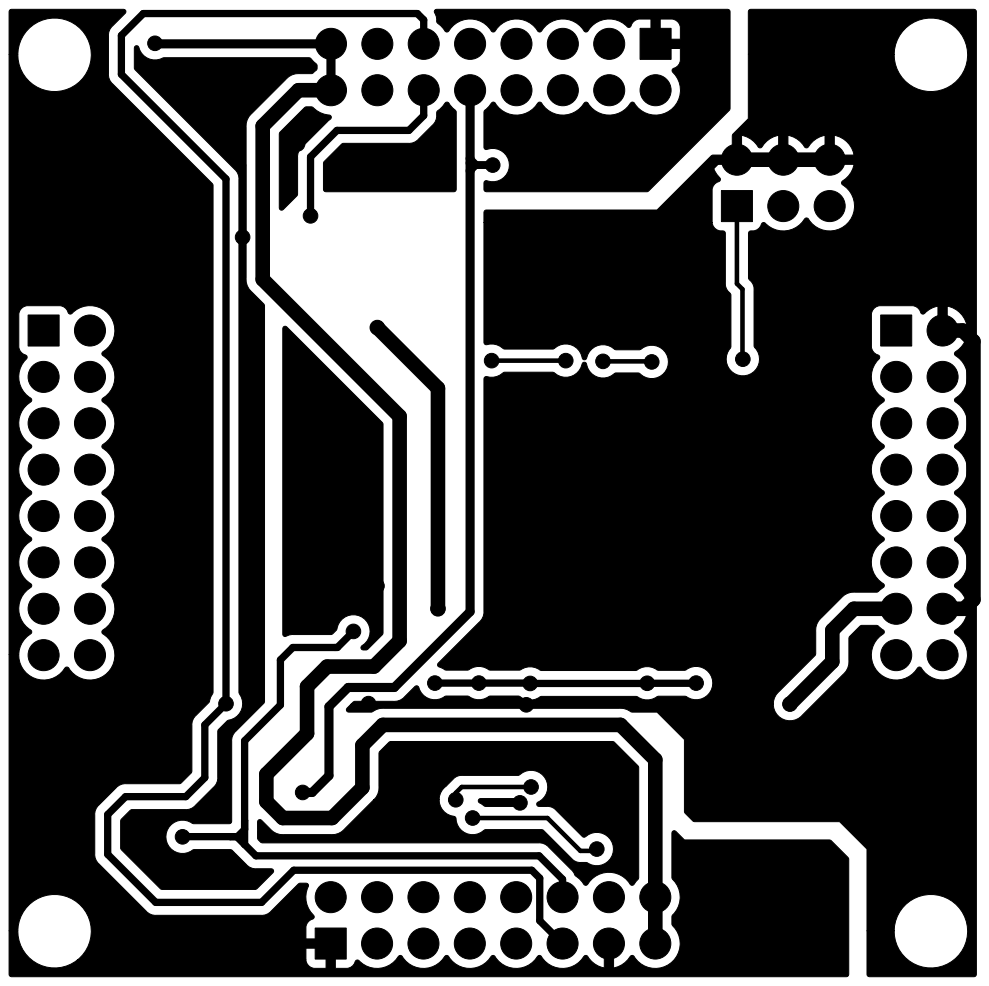
[picture p46: page 1]
