iotvertebrae/modules/hardware/pcbDesign/fabAnalogVertebra/pdf/vertExpI2c_00-B_Mask.pdf

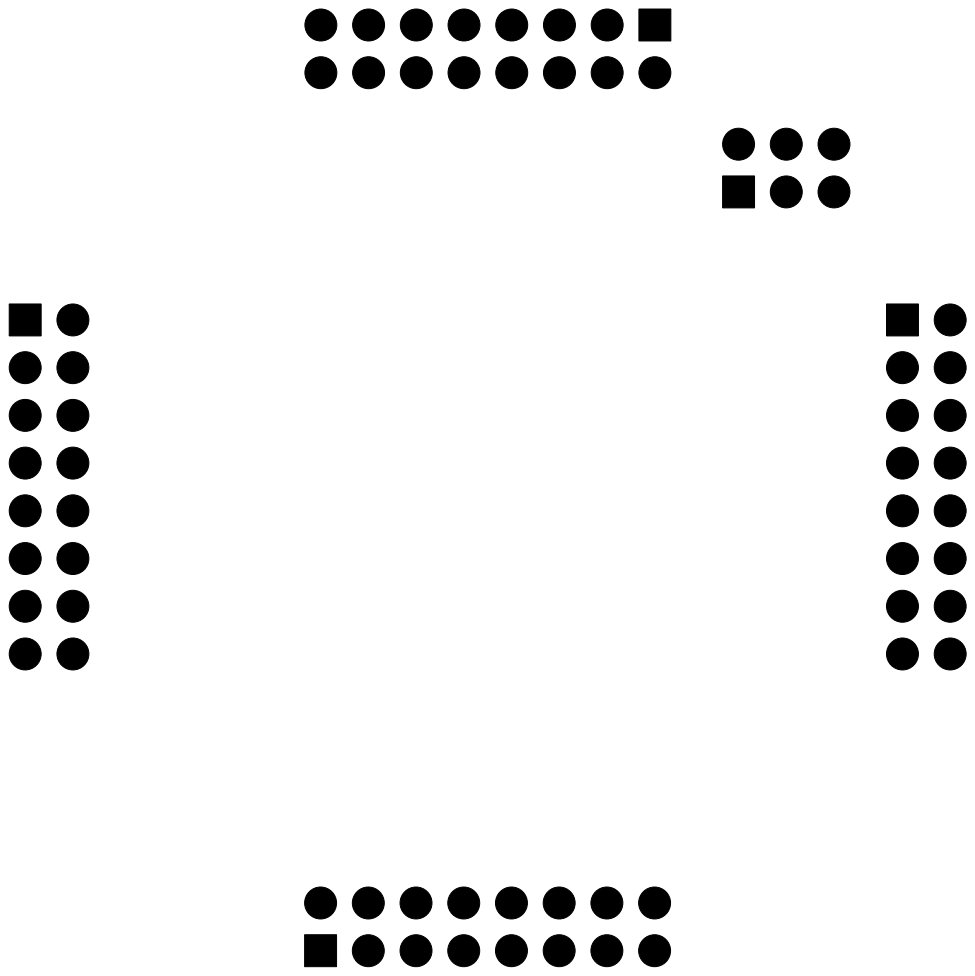
[picture p47: page 1]
