iotvertebrae/modules/hardware/pcbDesign/fabAnalogVertebra/pdf/vertExpI2c_00-Edge_Cuts.pdf

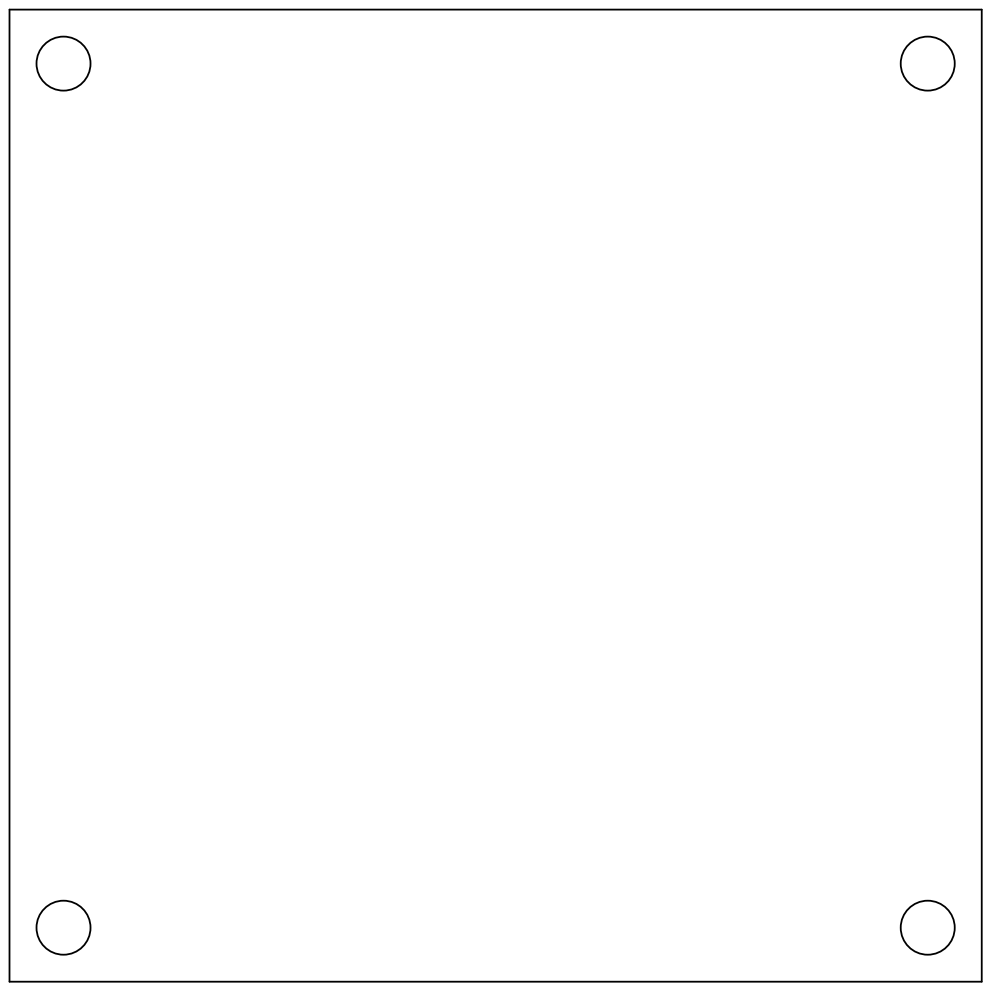
[picture p48: page 1]
