iotvertebrae/modules/hardware/pcbDesign/fabAnalogVertebra/pdf/vertExpI2c_00-F_Cu.pdf

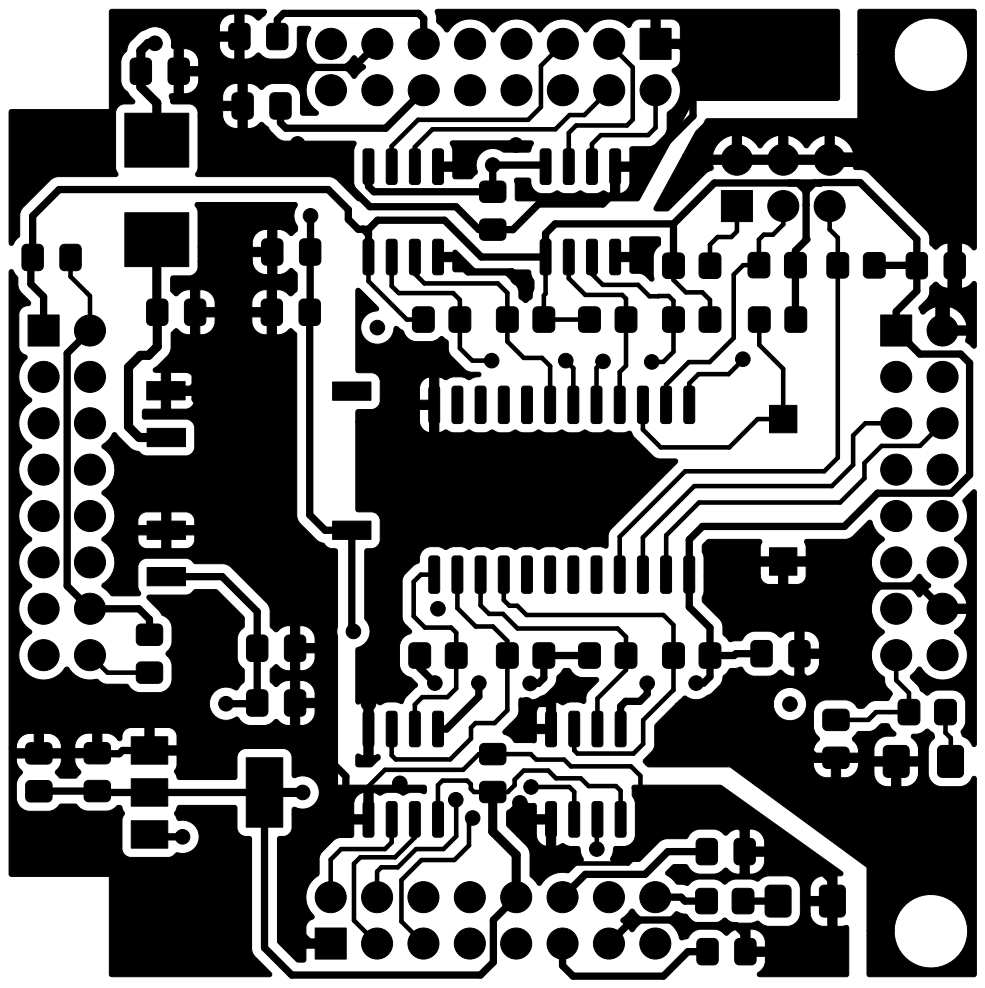
[picture p49: page 1]
