iotvertebrae/modules/hardware/pcbDesign/fabAnalogVertebra/pdf/vertExpI2c_00-F_Mask.pdf

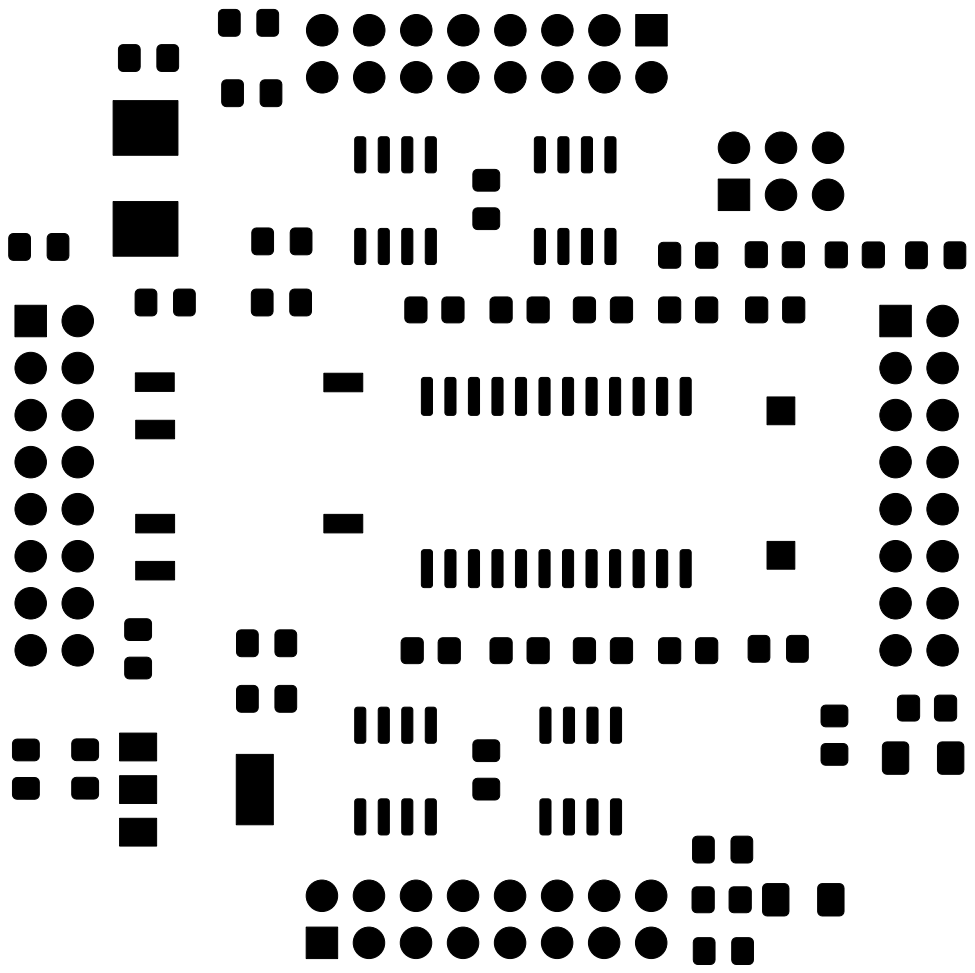
[picture p50: page 1]
