iotvertebrae/modules/hardware/pcbDesign/fabAnalogVertebra/pdf/vertExpI2c_00-F_Paste.pdf

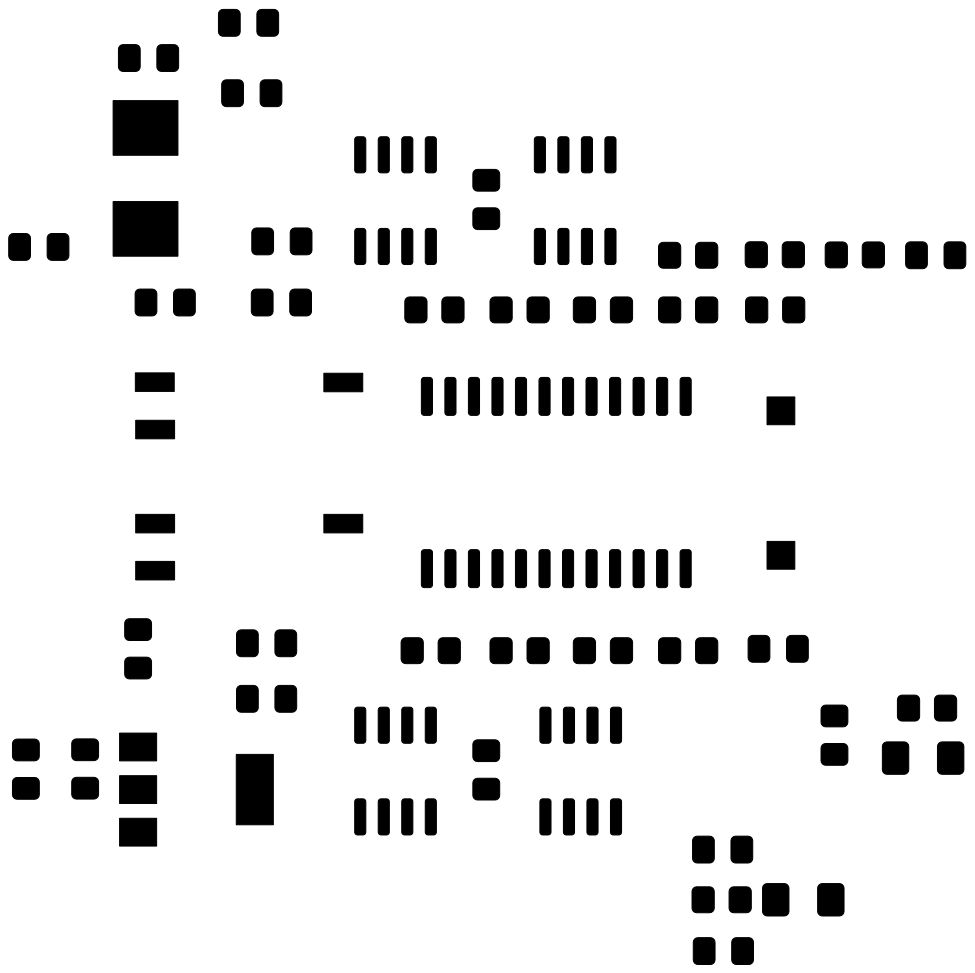
[picture p51: page 1]
