iotvertebrae/modules/hardware/pcbDesign/fabAnalogVertebra/pdf/vertExpI2c_00-F_Silkscreen.pdf

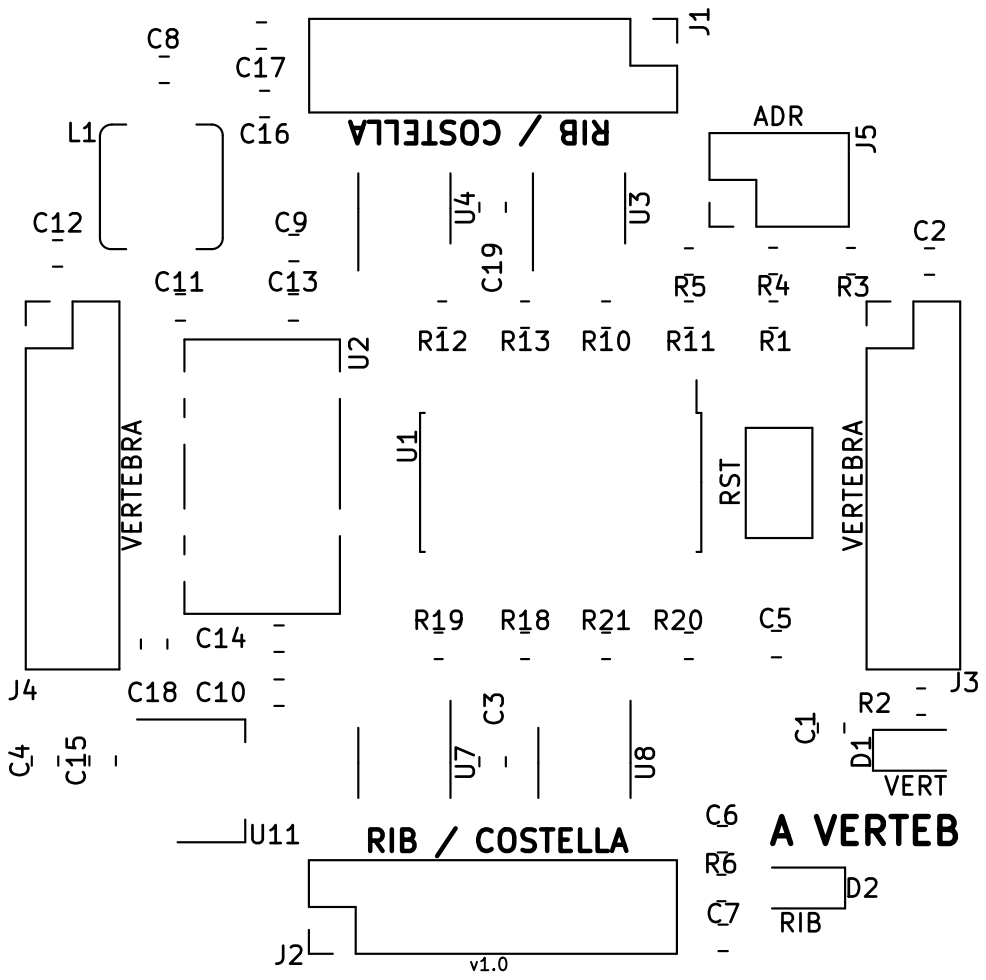
[picture p52: page 1]
