iotvertebrae/modules/hardware/pcbDesign/fabAnalogVertebra/pdf/vertExpI2c_00-In1_Cu.pdf

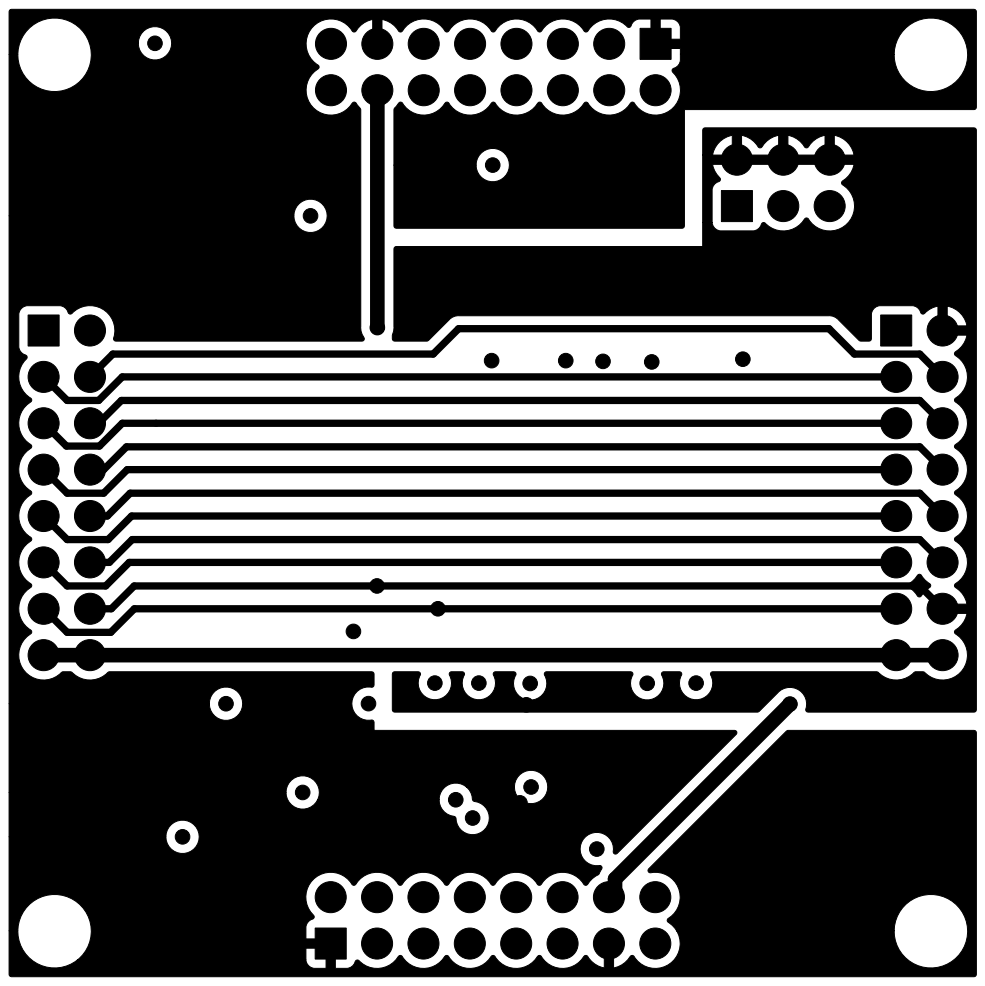
[picture p53: page 1]
