iotvertebrae/modules/hardware/pcbDesign/fabAnalogVertebra/pdf/vertExpI2c_00-In2_Cu.pdf

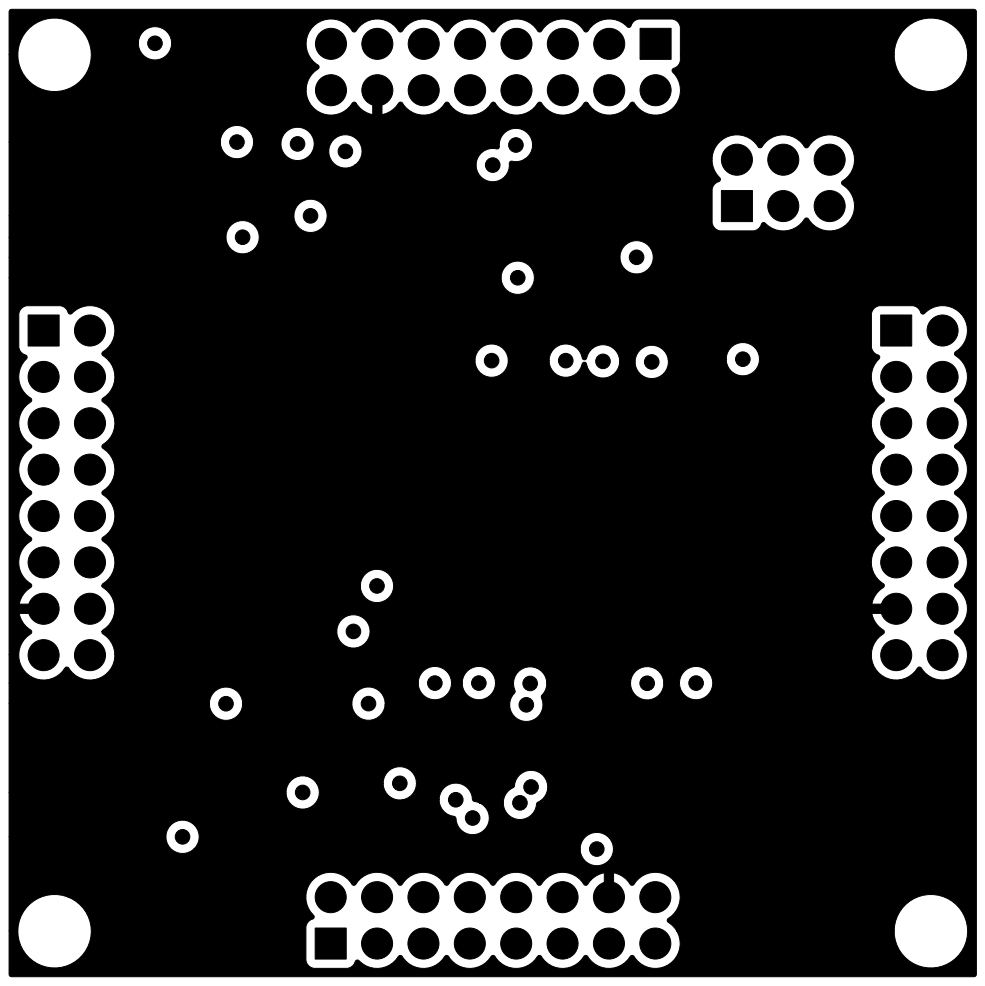
[picture p54: page 1]
