iotvertebrae/modules/hardware/pcbDesign/fabDacRib/pdf/rib4outAd_00-B_Cu.pdf

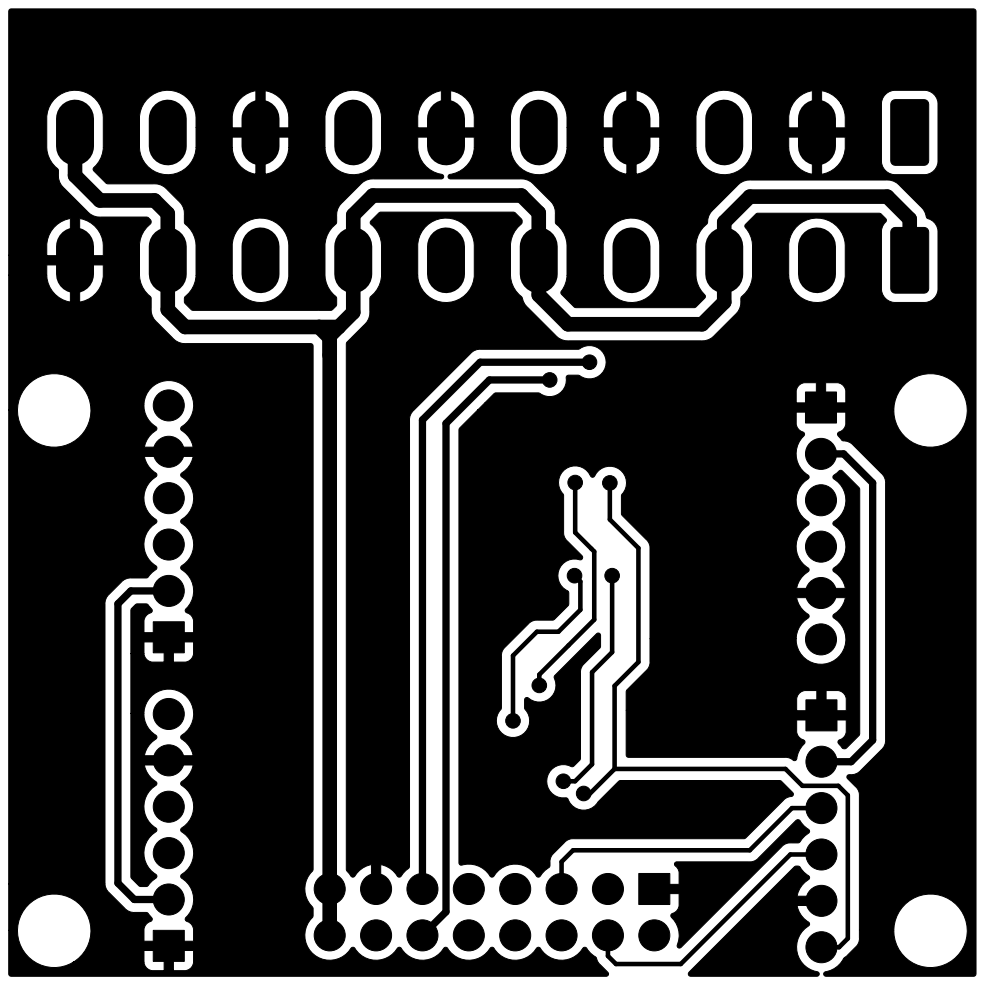
[picture p55: page 1]
