iotvertebrae/modules/hardware/pcbDesign/fabDacRib/pdf/rib4outAd_00-B_Mask.pdf

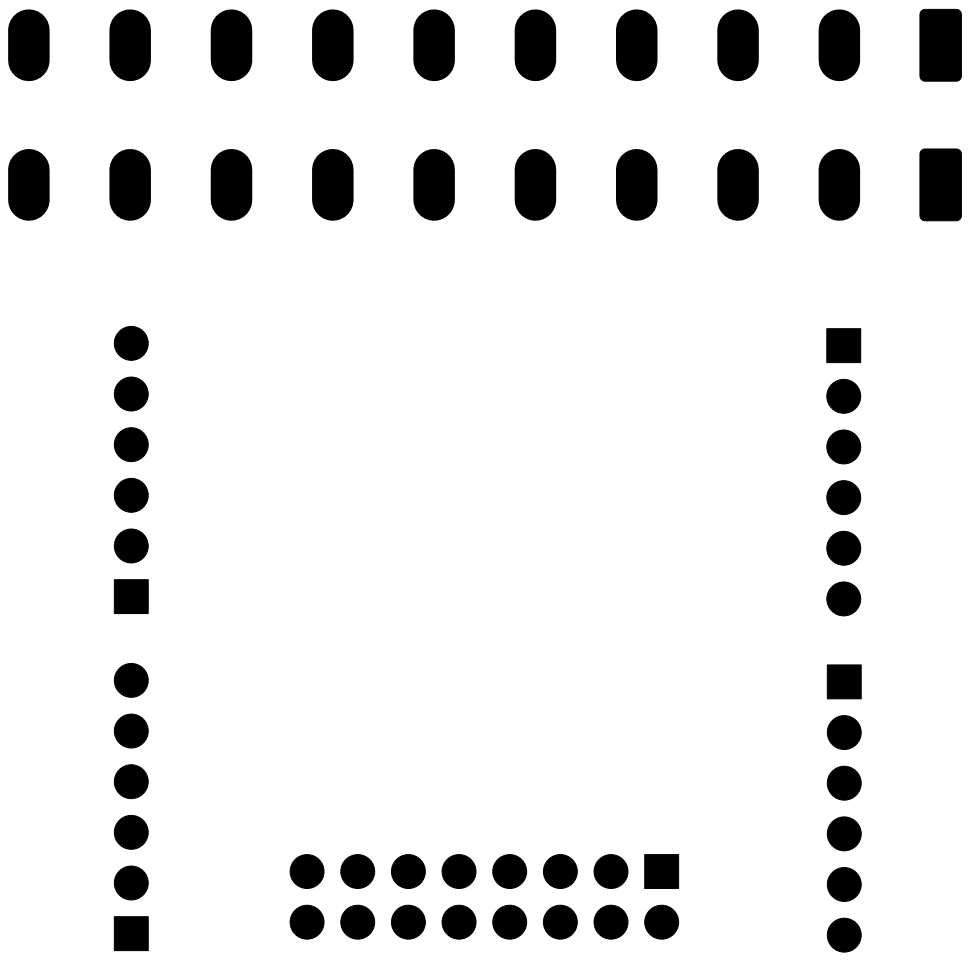
[picture p56: page 1]
