iotvertebrae/modules/hardware/pcbDesign/fabDacRib/pdf/rib4outAd_00-Edge_Cuts.pdf

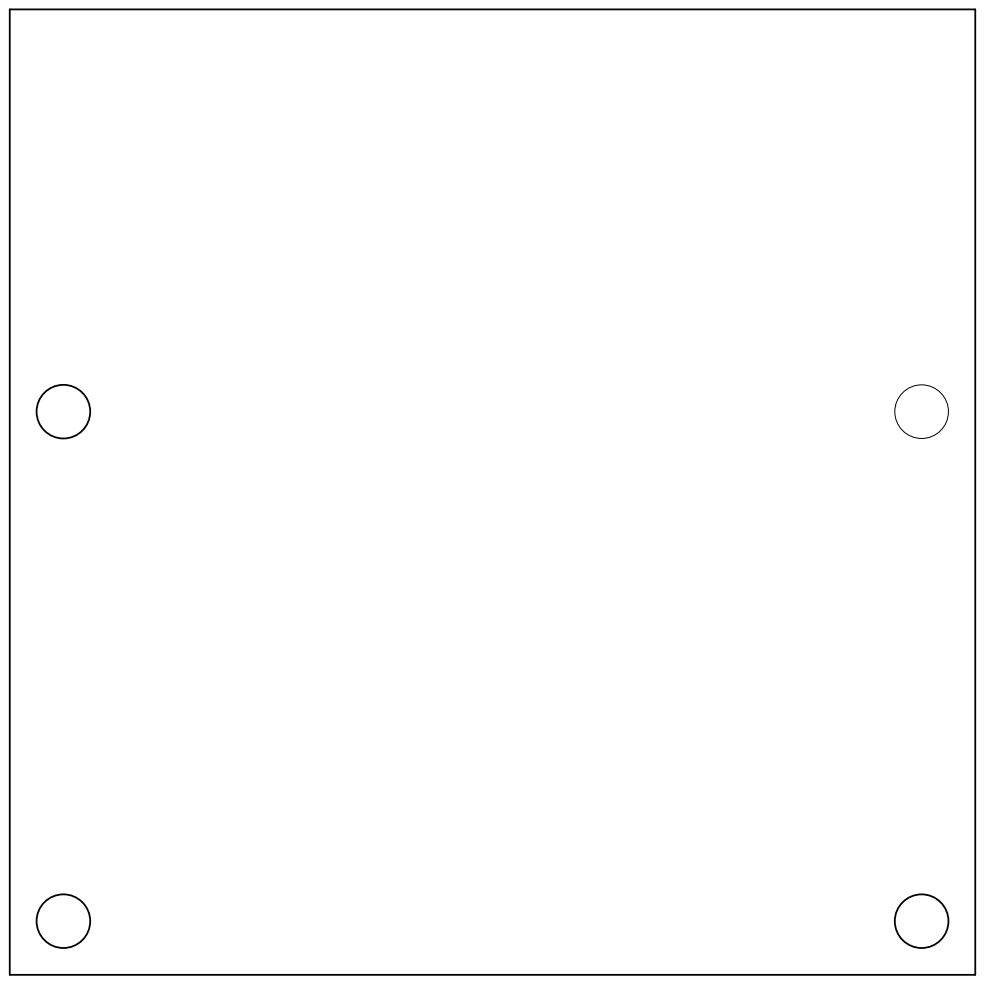
[picture p57: page 1]
