iotvertebrae/modules/hardware/pcbDesign/fabDacRib/pdf/rib4outAd_00-F_Cu.pdf

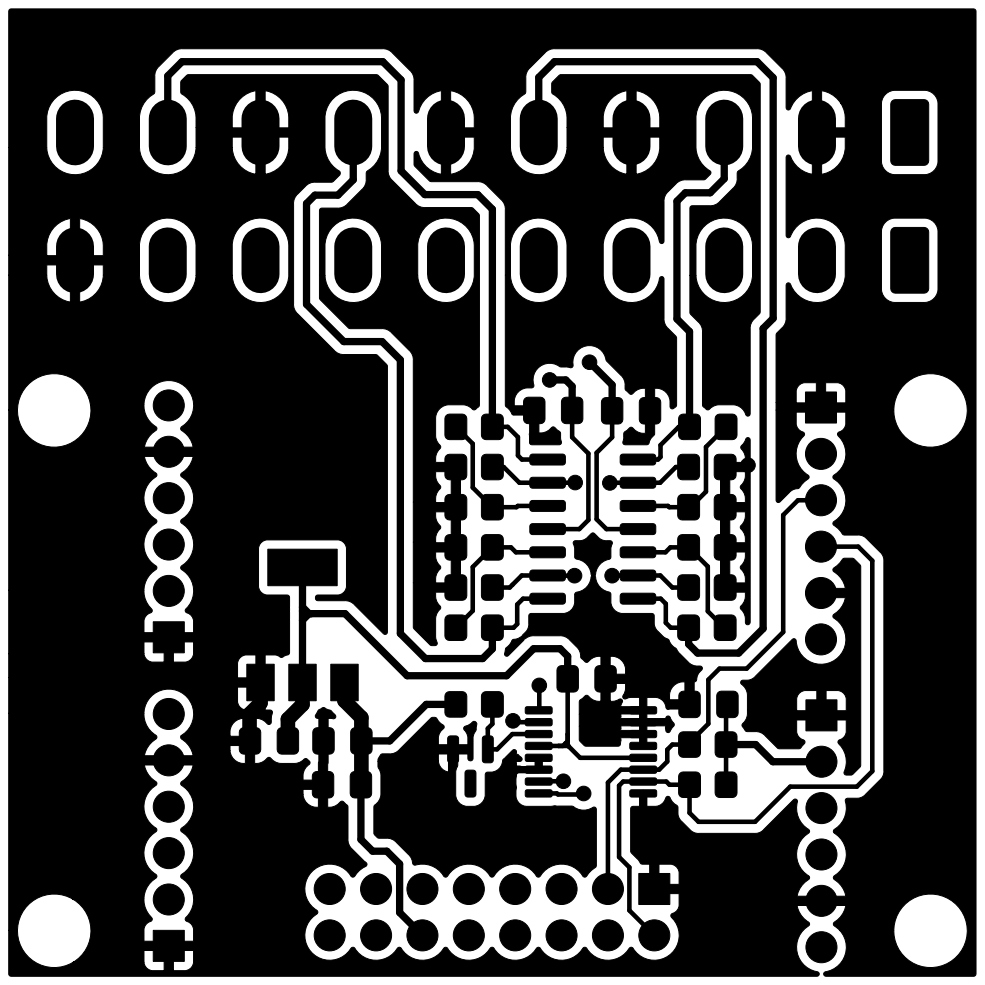
[picture p58: page 1]
