iotvertebrae/modules/hardware/pcbDesign/fabDacRib/pdf/rib4outAd_00-F_Mask.pdf

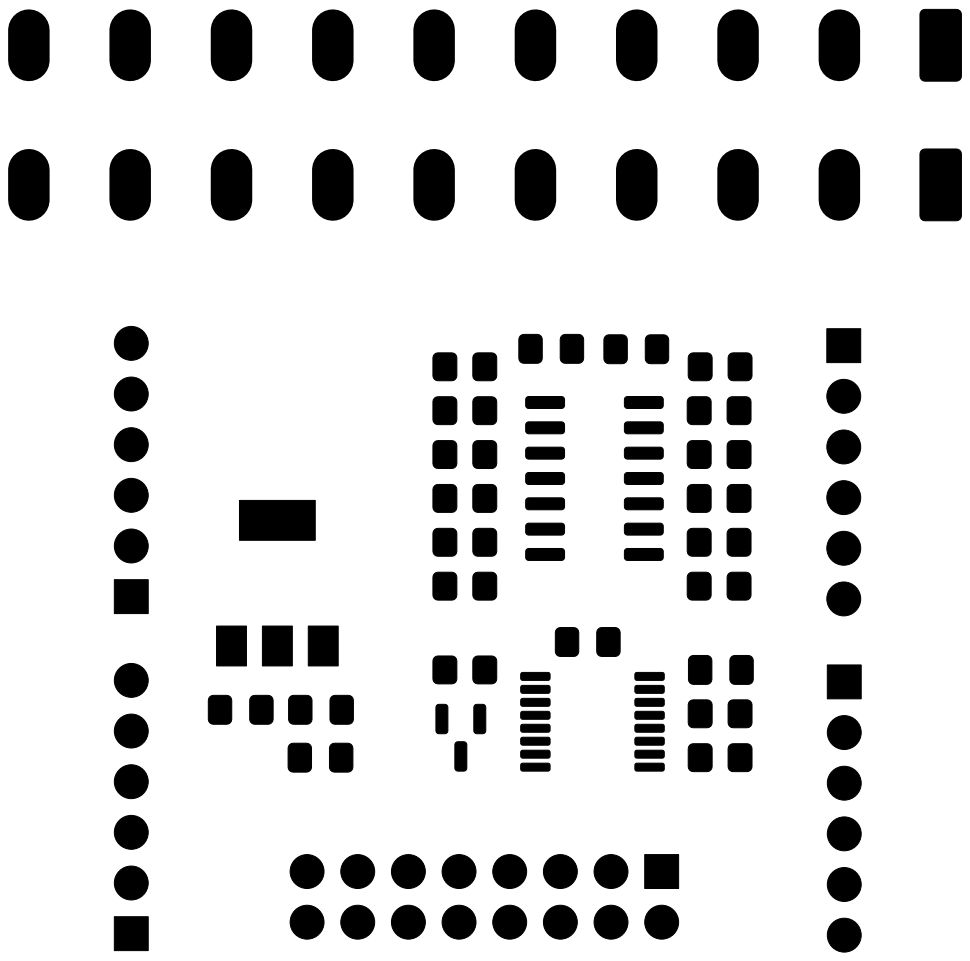
[picture p59: page 1]
