iotvertebrae/modules/hardware/pcbDesign/fabDacRib/pdf/rib4outAd_00-F_Paste.pdf

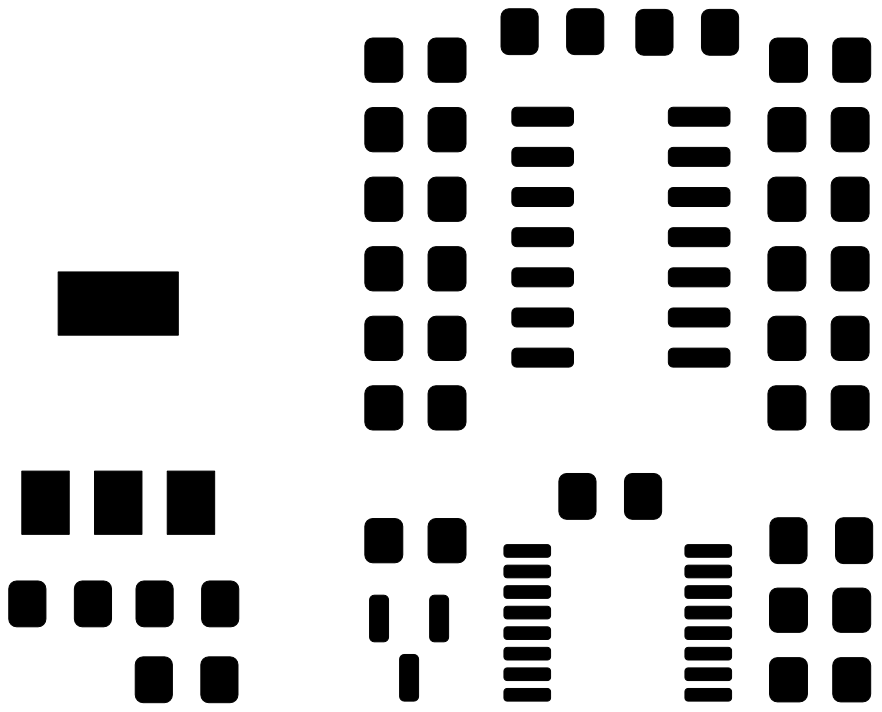
[picture p60: page 1]
