iotvertebrae/modules/hardware/pcbDesign/fabDacRib/pdf/rib4outAd_00-F_Silkscreen.pdf

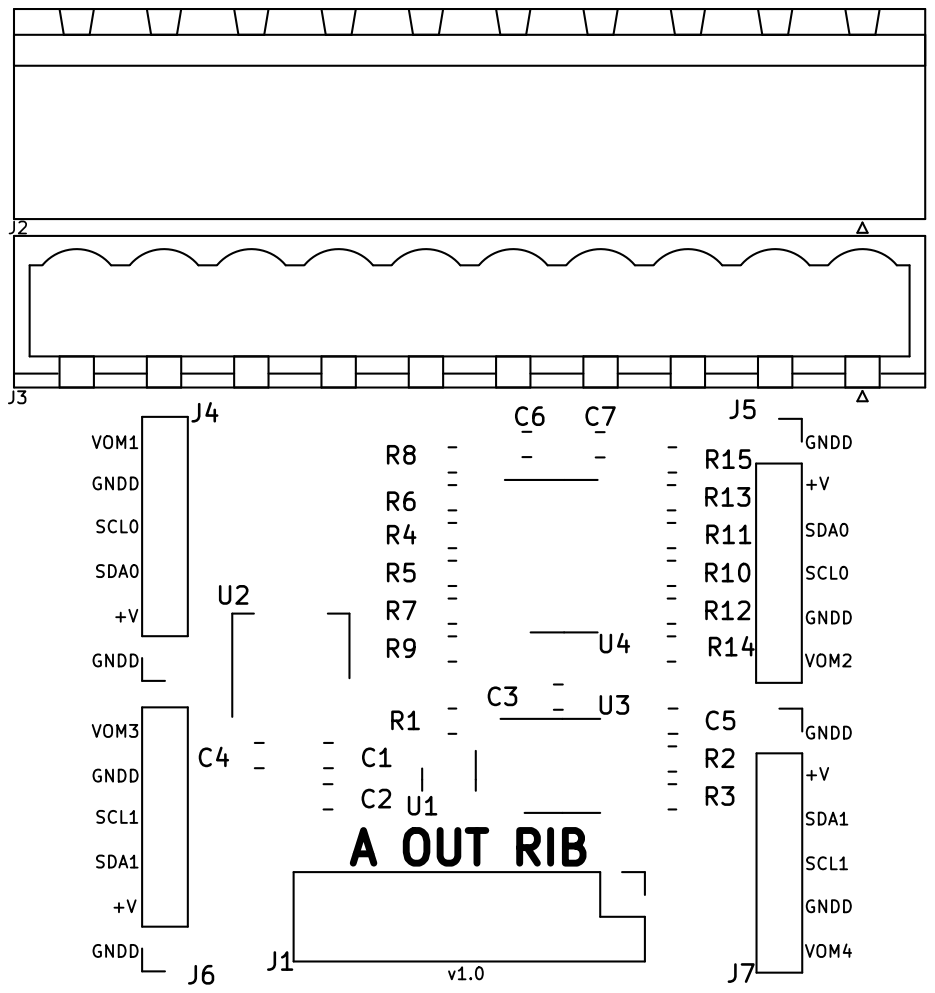
[picture p61: page 1]
