iotvertebrae/modules/hardware/pcbDesign/fabDacRib/pdf/rib4outAd_00-In1_Cu.pdf

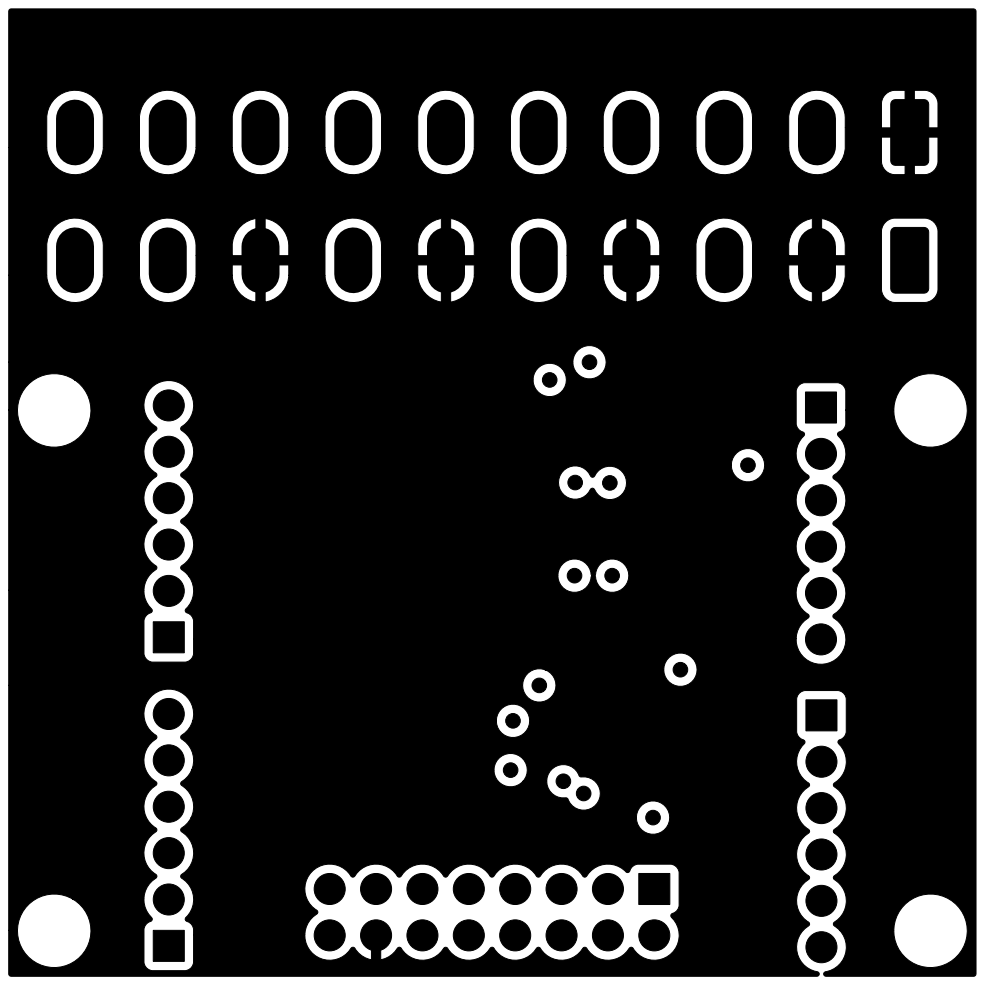
[picture p62: page 1]
