iotvertebrae/modules/hardware/pcbDesign/fabDacRib/pdf/rib4outAd_00-In2_Cu.pdf

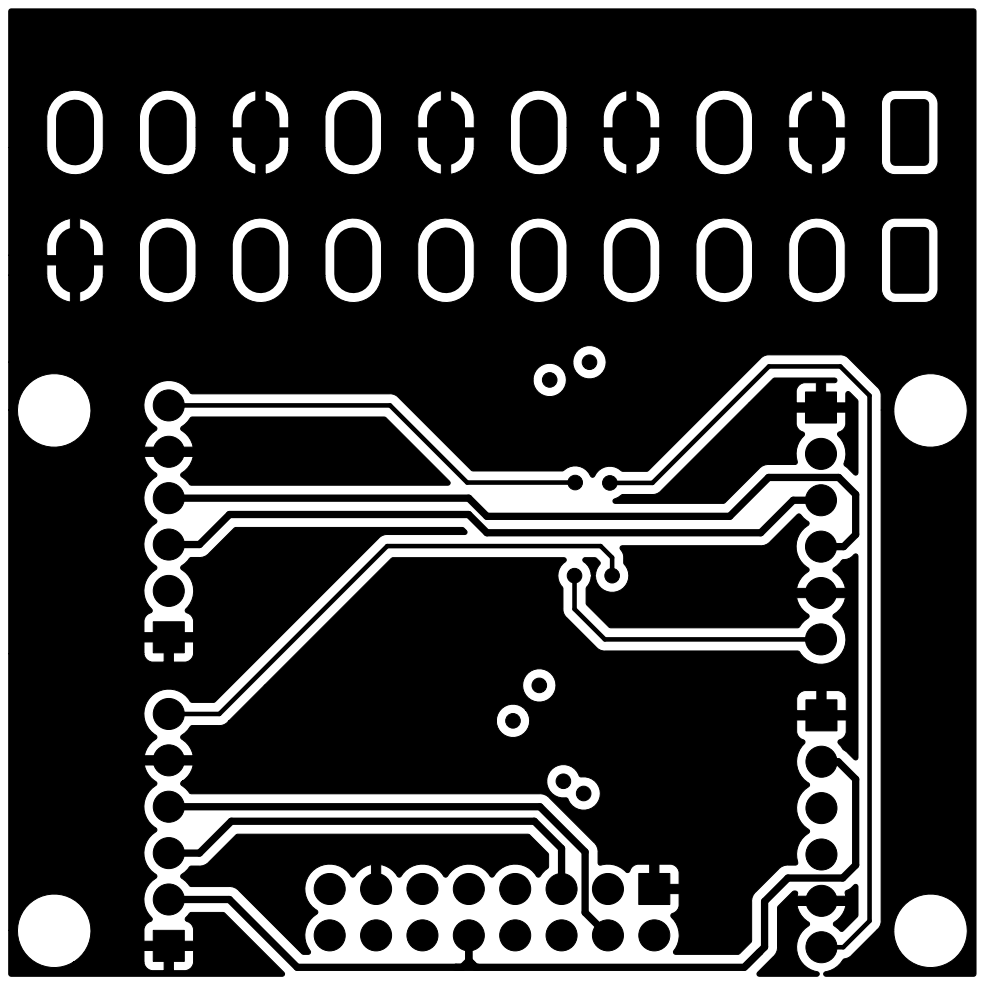
[picture p63: page 1]
