iotvertebrae/modules/hardware/pcbDesign/v2.0/gerbers/avert20/pdf/avert_12-B_Cu.pdf

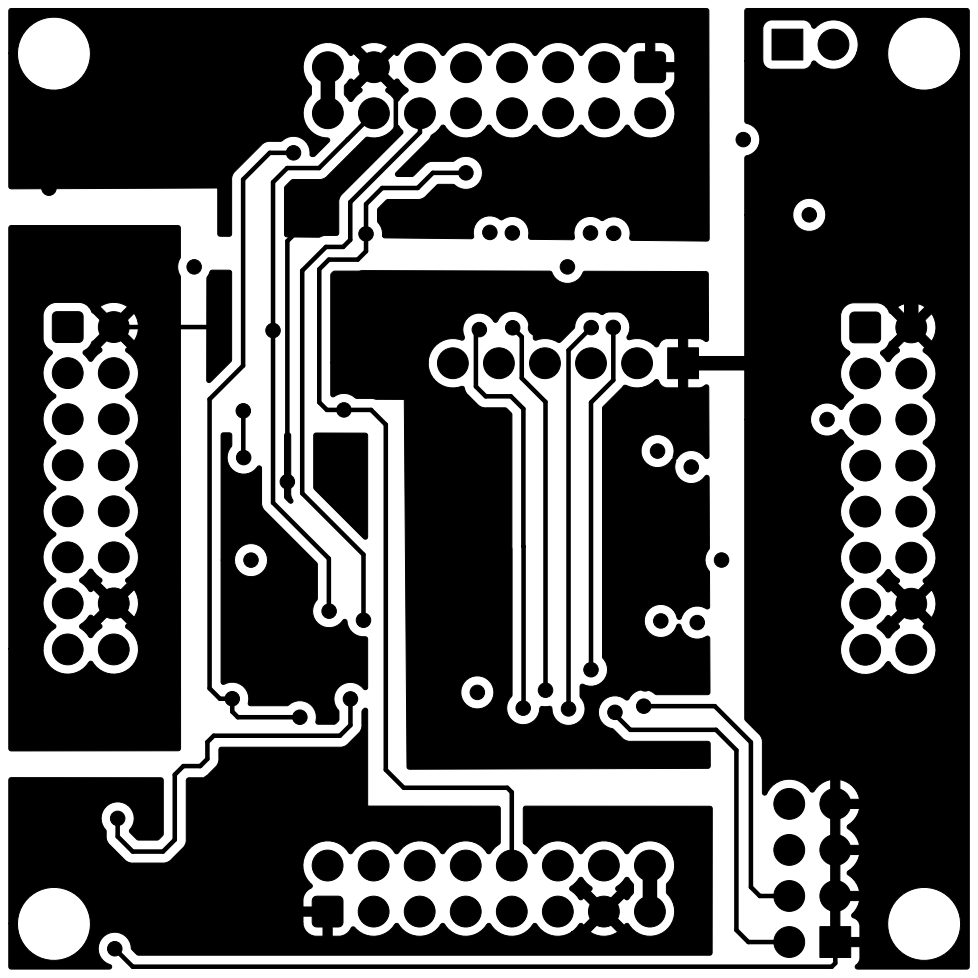
[picture p64: page 1]
