iotvertebrae/modules/hardware/pcbDesign/v2.0/gerbers/avert20/pdf/avert_12-B_Mask.pdf

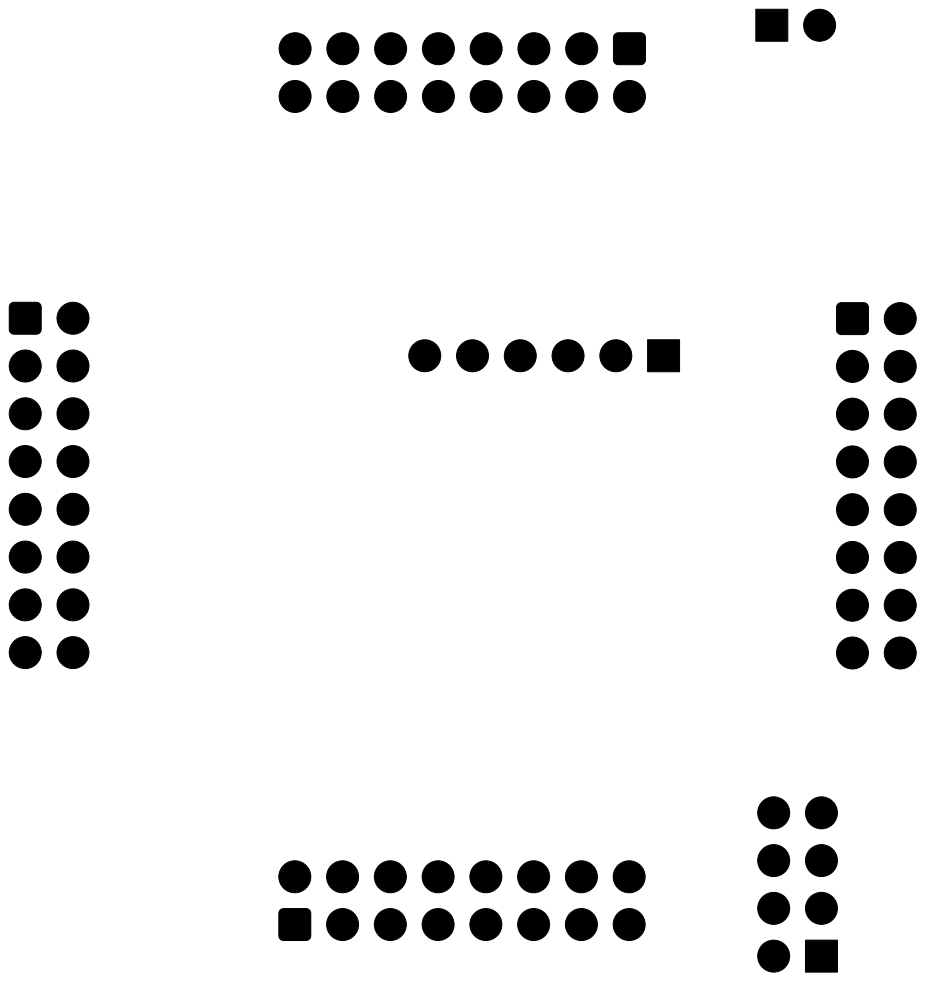
[picture p65: page 1]
