iotvertebrae/modules/hardware/pcbDesign/v2.0/gerbers/avert20/pdf/avert_12-Edge_Cuts.pdf

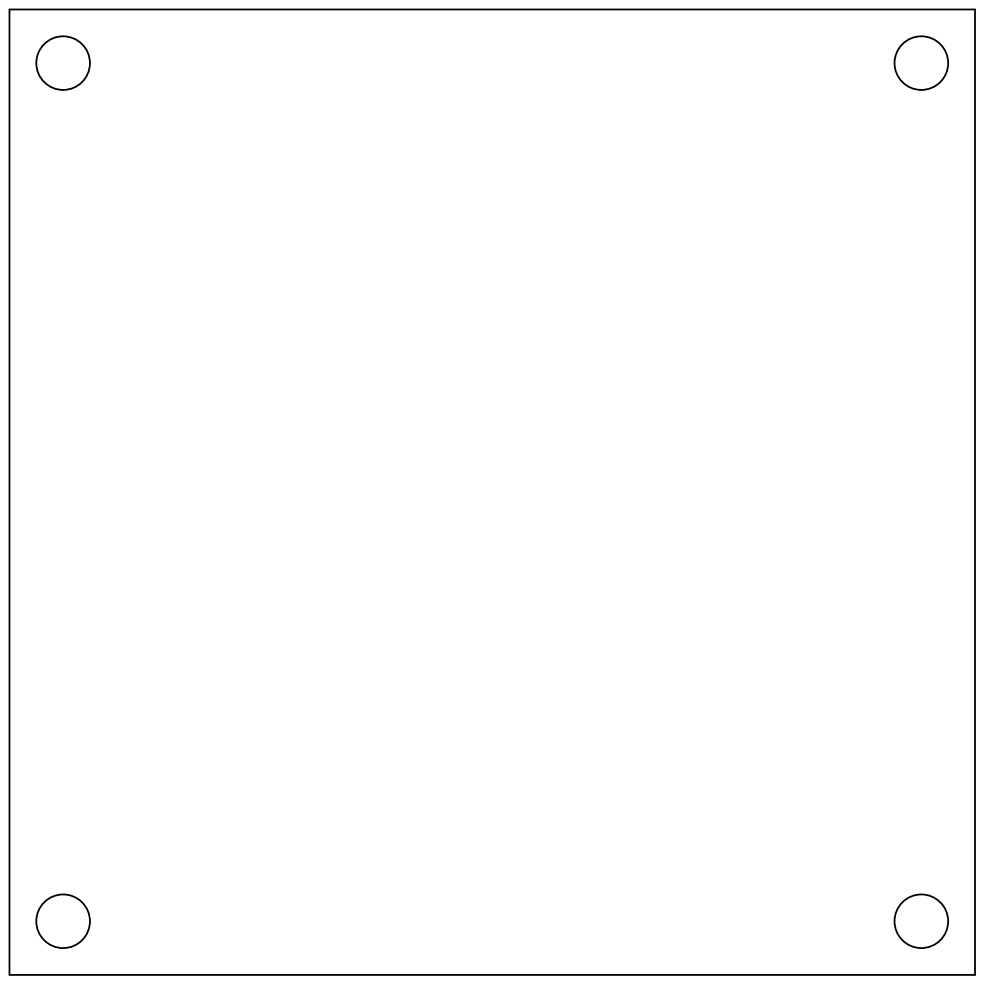
[picture p66: page 1]
