iotvertebrae/modules/hardware/pcbDesign/v2.0/gerbers/avert20/pdf/avert_12-F_Cu.pdf

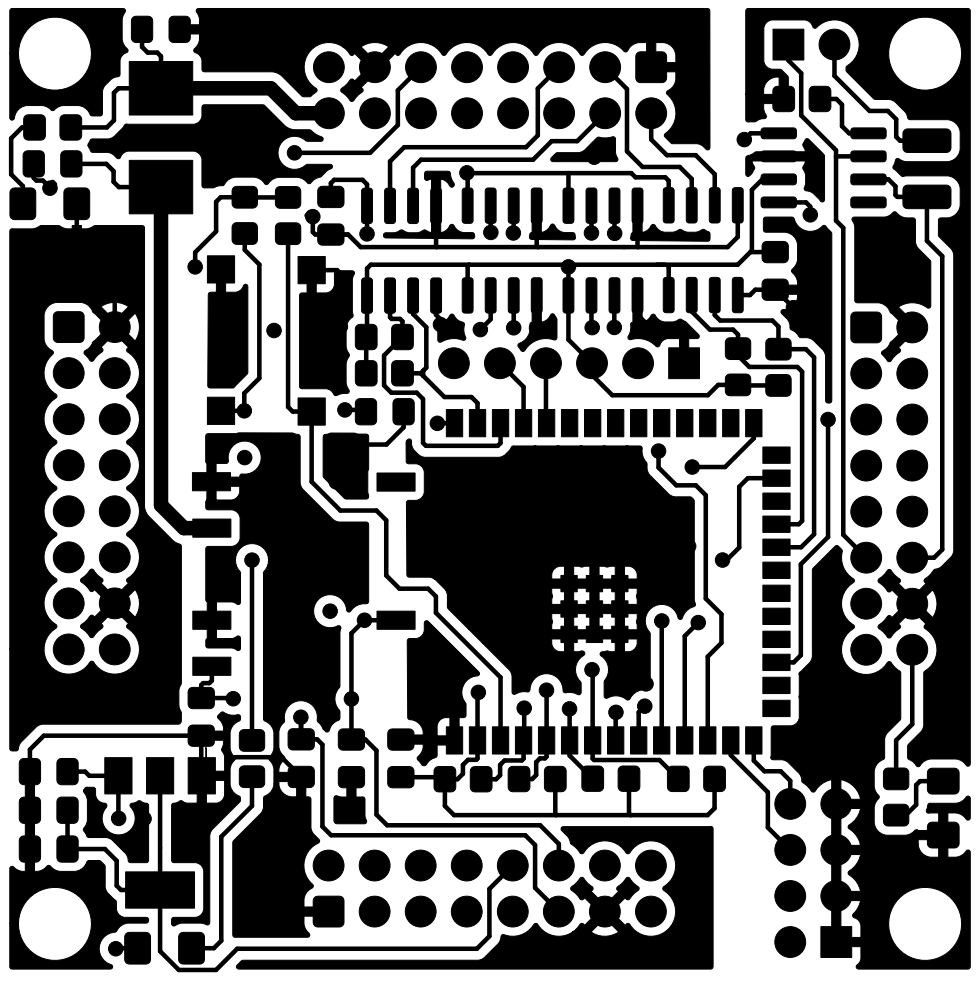
[picture p67: page 1]
