iotvertebrae/modules/hardware/pcbDesign/v2.0/gerbers/avert20/pdf/avert_12-F_Mask.pdf

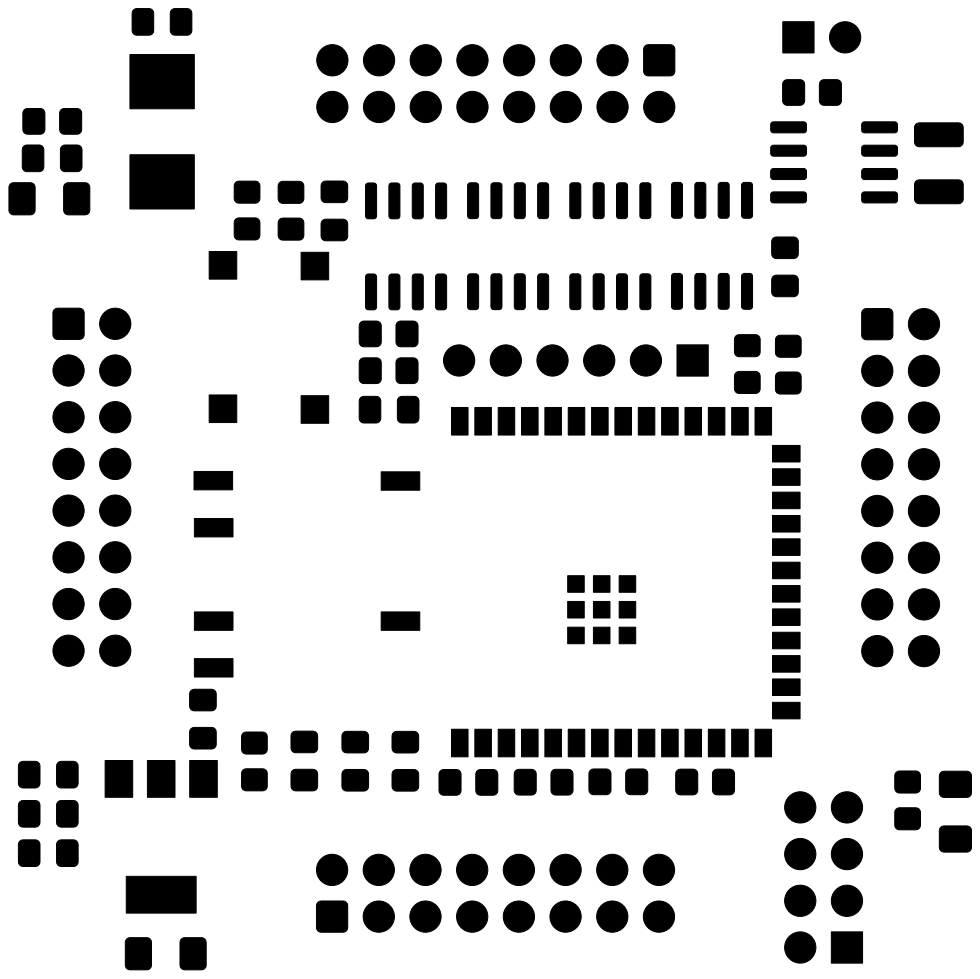
[picture p68: page 1]
