iotvertebrae/modules/hardware/pcbDesign/v2.0/gerbers/avert20/pdf/avert_12-F_Paste.pdf

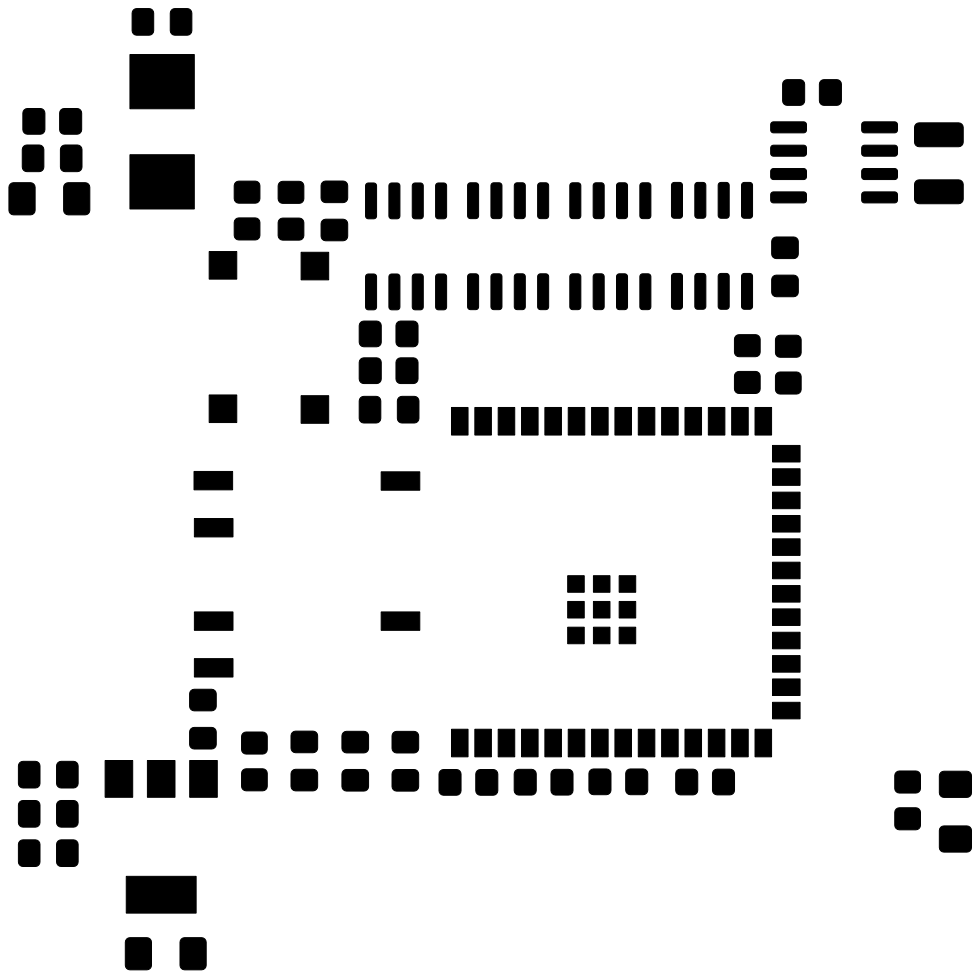
[picture p69: page 1]
