iotvertebrae/modules/hardware/pcbDesign/v2.0/gerbers/avert20/pdf/avert_12-F_Silkscreen.pdf

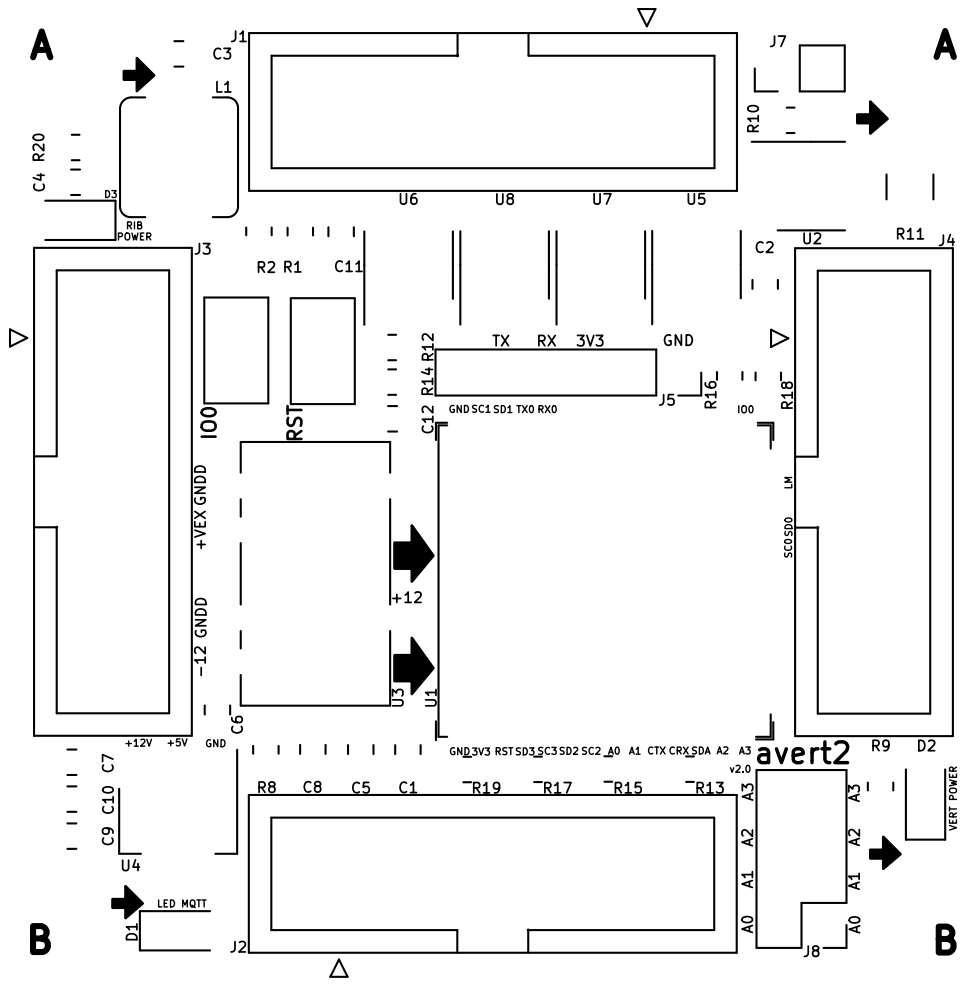
[picture p70: page 1]
