iotvertebrae/modules/hardware/pcbDesign/v2.0/gerbers/avert20/pdf/avert_12-In1_Cu.pdf

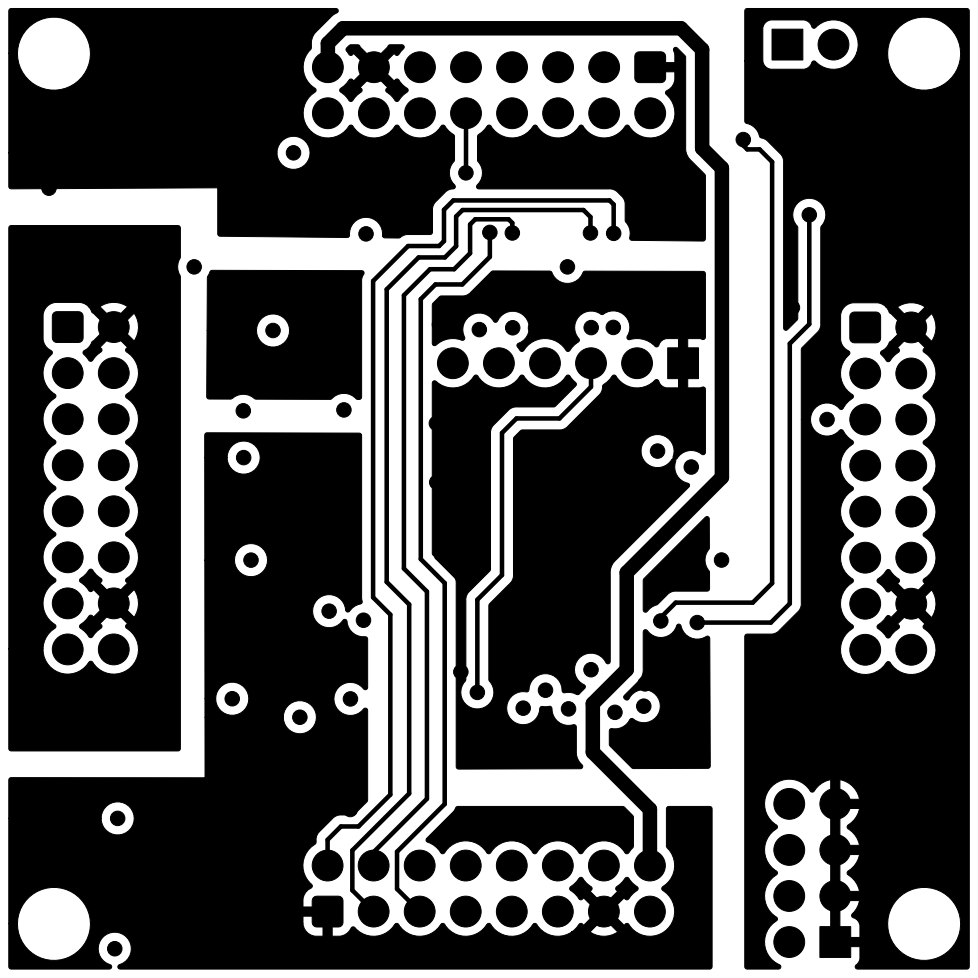
[picture p71: page 1]
