iotvertebrae/modules/hardware/pcbDesign/v2.0/gerbers/avert20/pdf/avert_12-In2_Cu.pdf

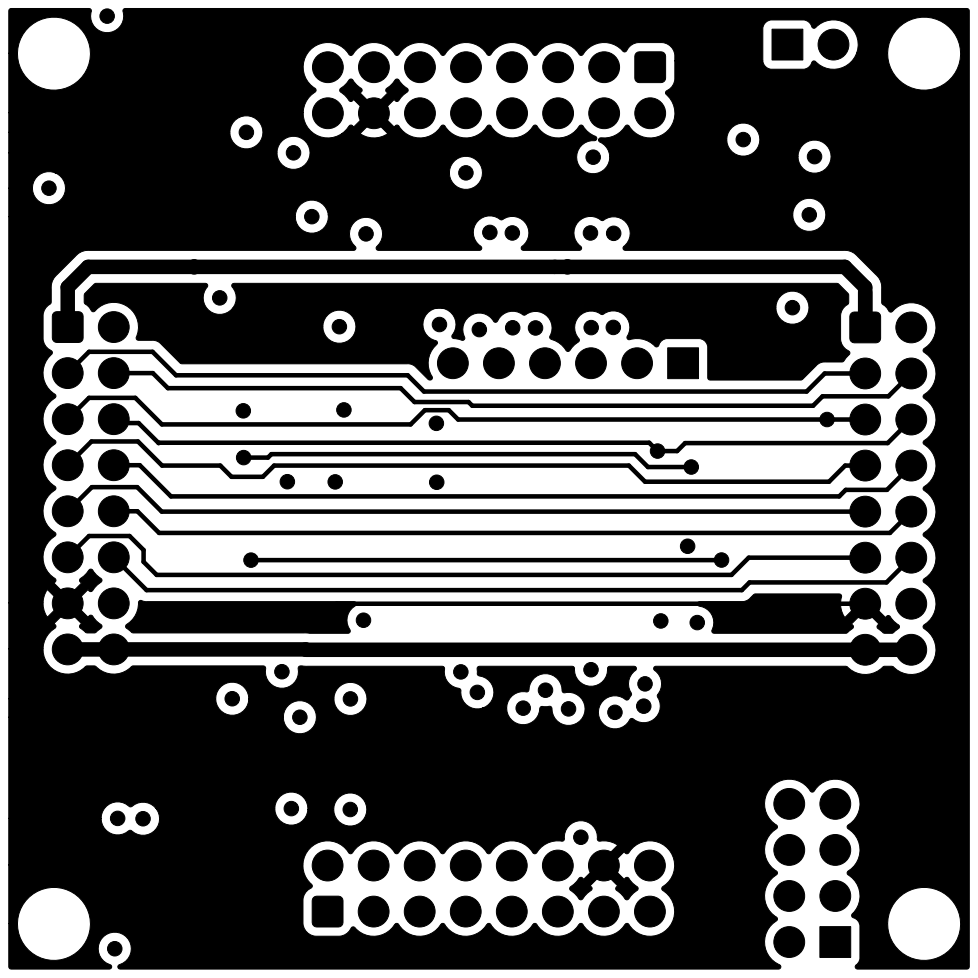
[picture p72: page 1]
