iotvertebrae/modules/hardware/pcbDesign/v2.0/gerbers/dvert20/pdf/dvert_12-B_Cu.pdf

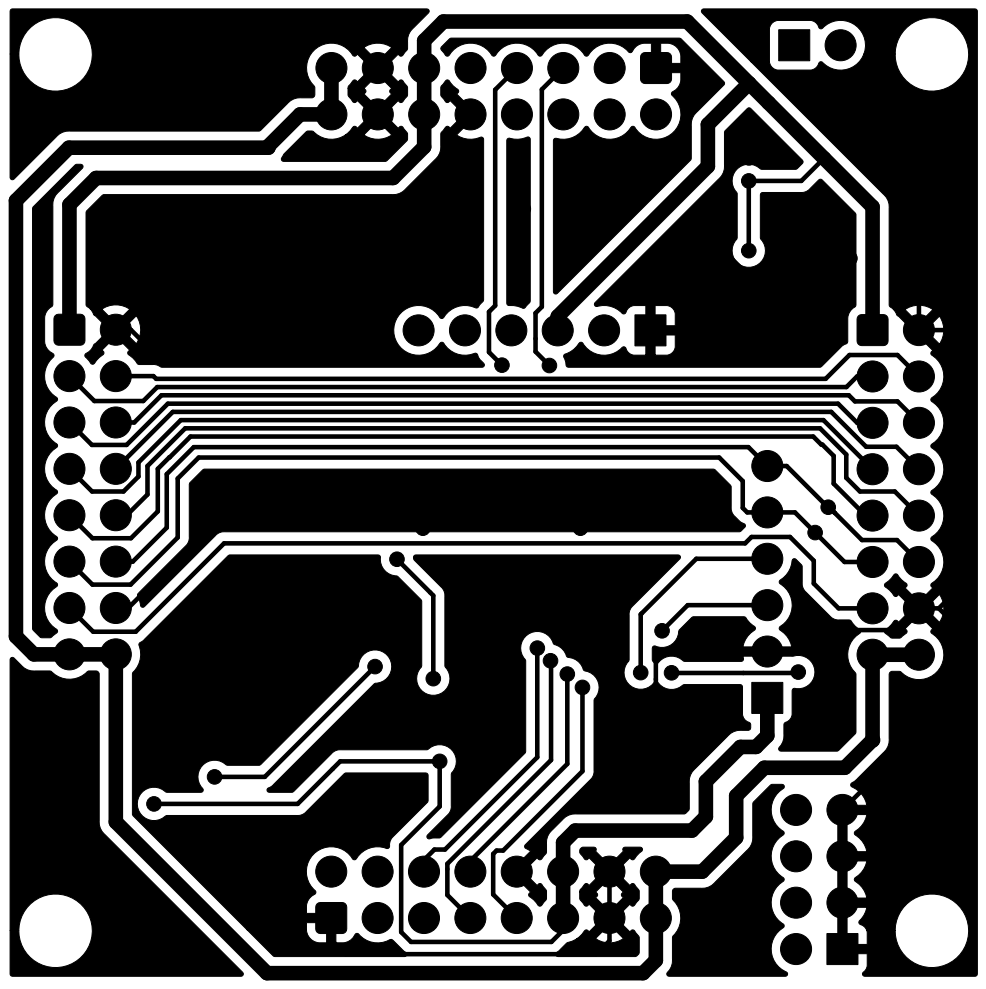
[picture p73: page 1]
